nightflyer88/CG_scale/data/CG_scale_mechanics.png

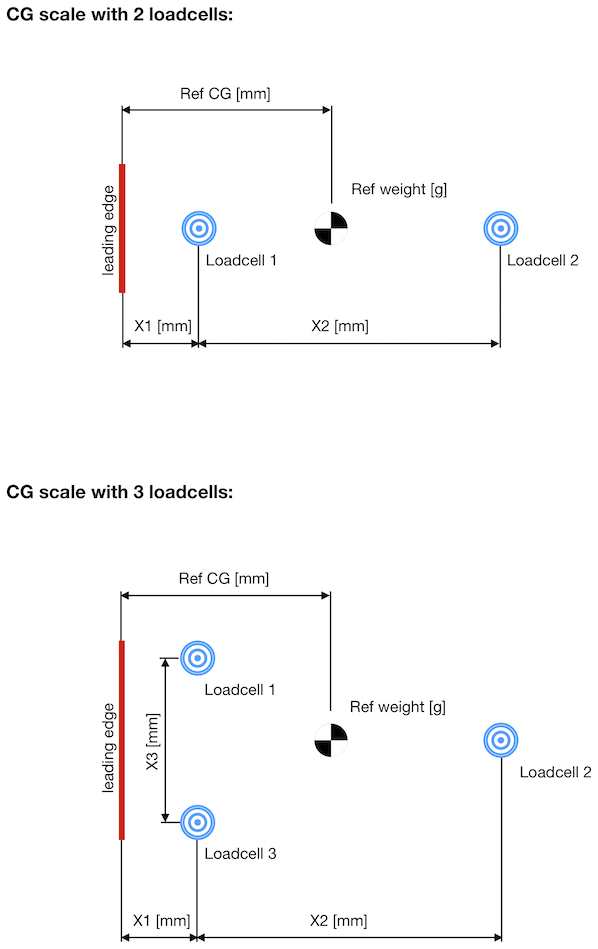
data/CG_scale_mechanics.png
