nightflyer88/CG_scale/data/pc6.png

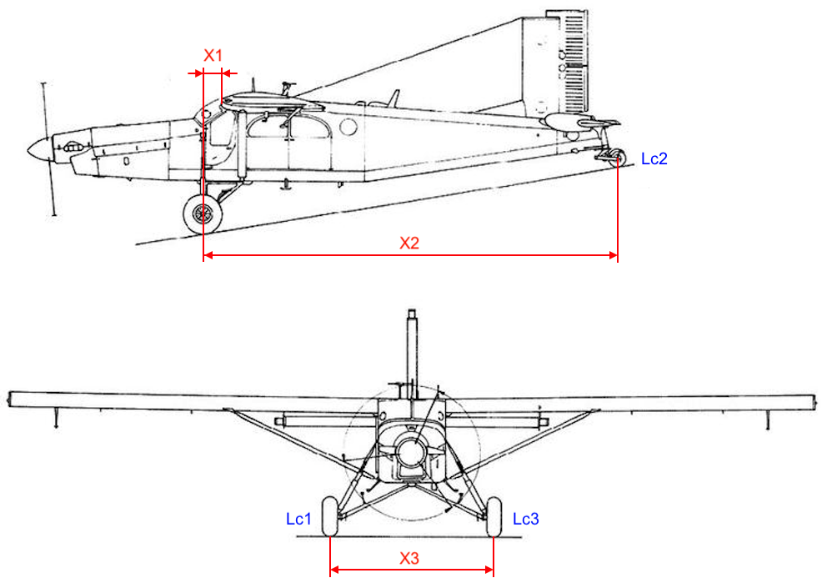
data/pc6.png
