nightflyer88/CG_scale/data/pc7.png

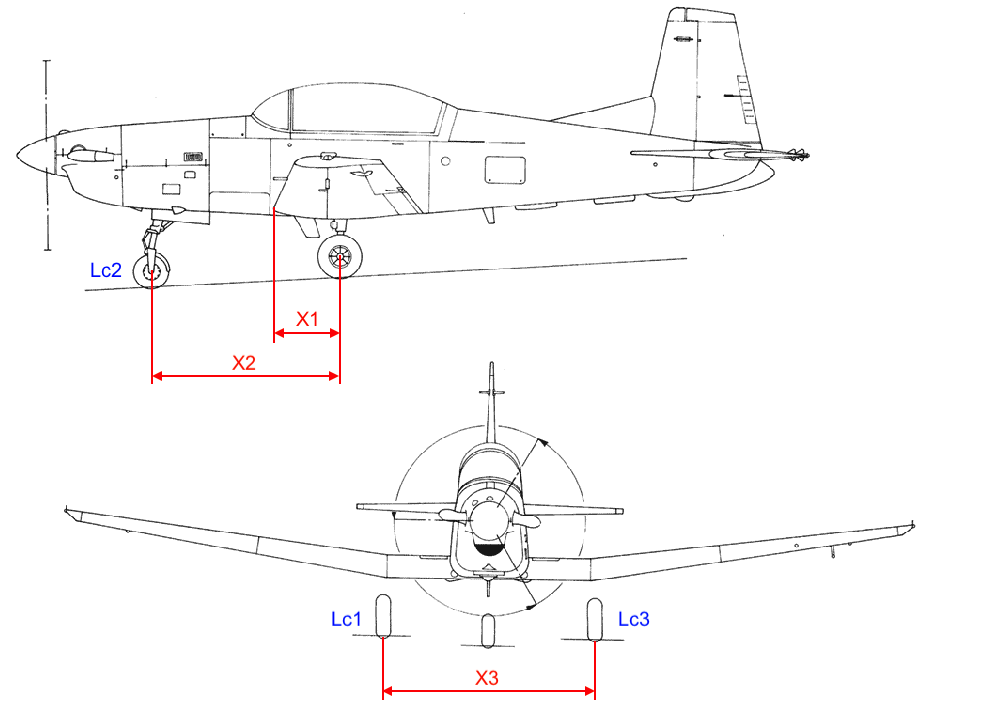
data/pc7.png
