nightflyer88/CG_scale/data/Resistor.png

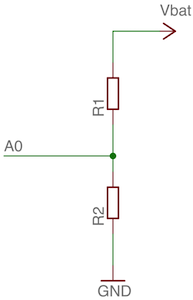
data/Resistor.png
