nightflyer88/CG_scale/Doc/Balance CPT 5mm/img/20180502_205738.jpg

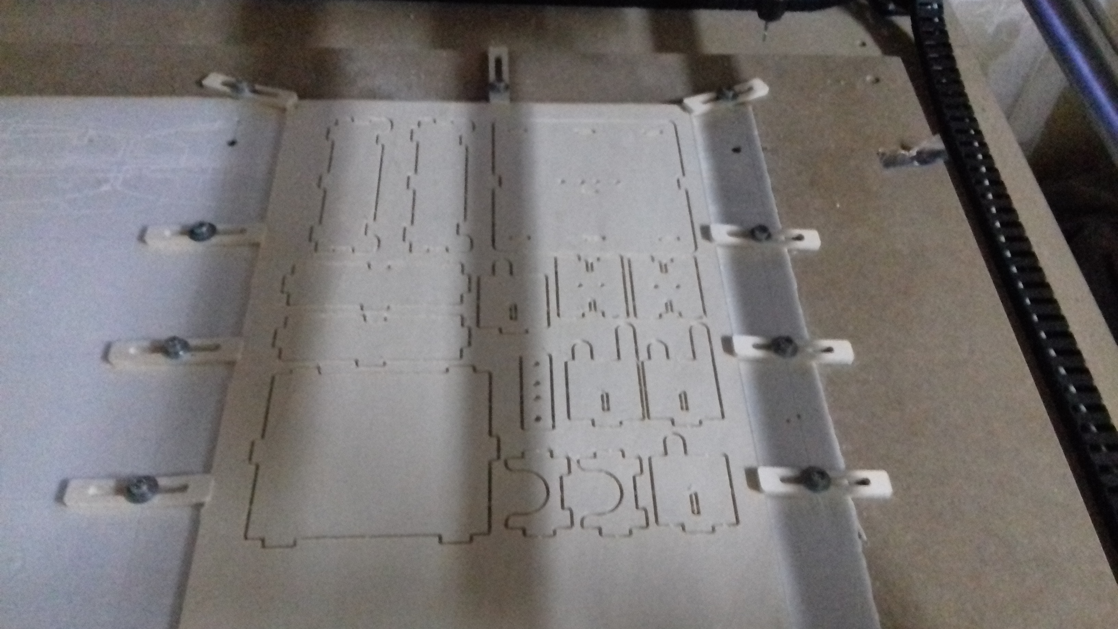
Doc/Balance CPT 5mm/img/20180502_205738.jpg
