nightflyer88/CG_scale/Doc/Balance CPT 5mm/img/20180502_213406.jpg

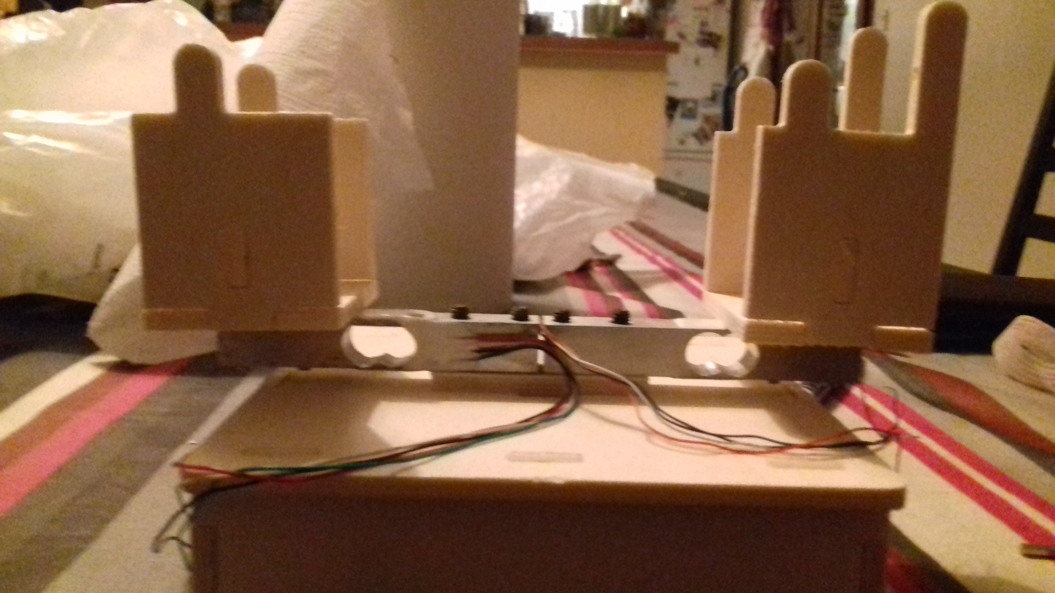
Doc/Balance CPT 5mm/img/20180502_213406.jpg
