nightflyer88/CG_scale/Doc/Balance CPT 5mm/img/20190110_205133.jpg

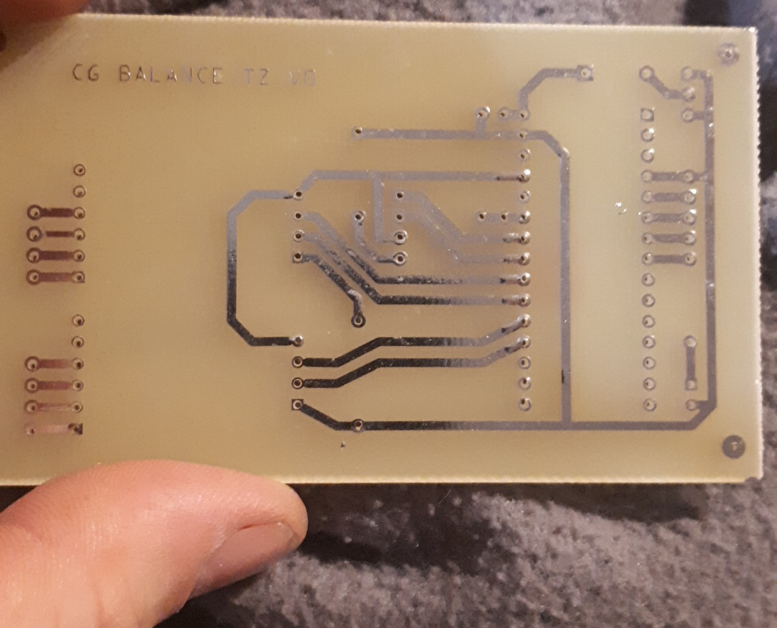
Doc/Balance CPT 5mm/img/20190110_205133.jpg
