nightflyer88/CG_scale/Doc/Balance CPT 5mm/img/20190118_182447.jpg

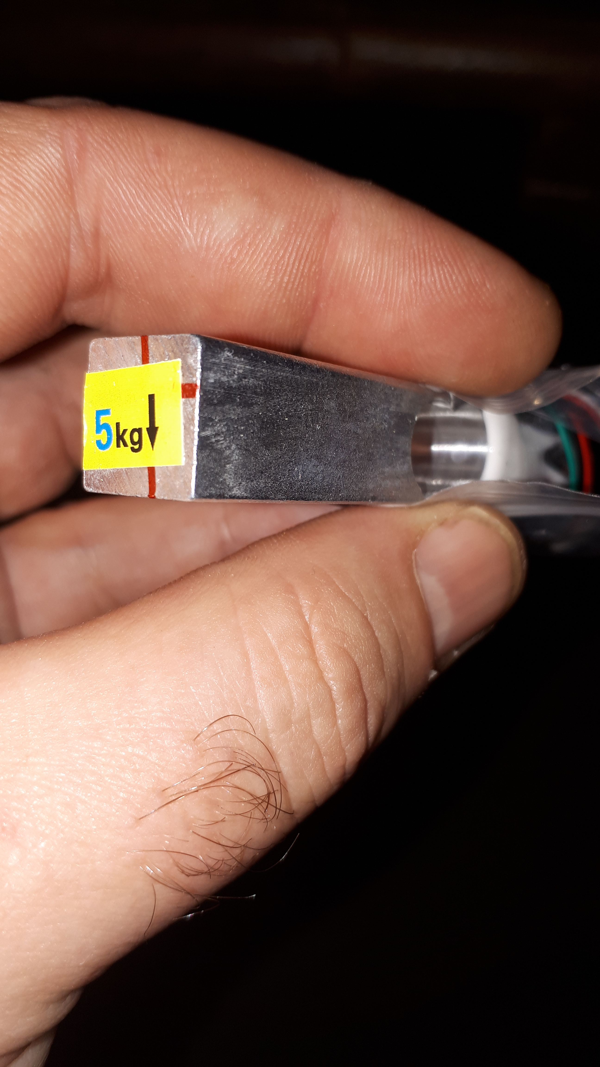
Doc/Balance CPT 5mm/img/20190118_182447.jpg
