nightflyer88/CG_scale/Doc/Balance CPT 5mm/img/20190121_222057.jpg

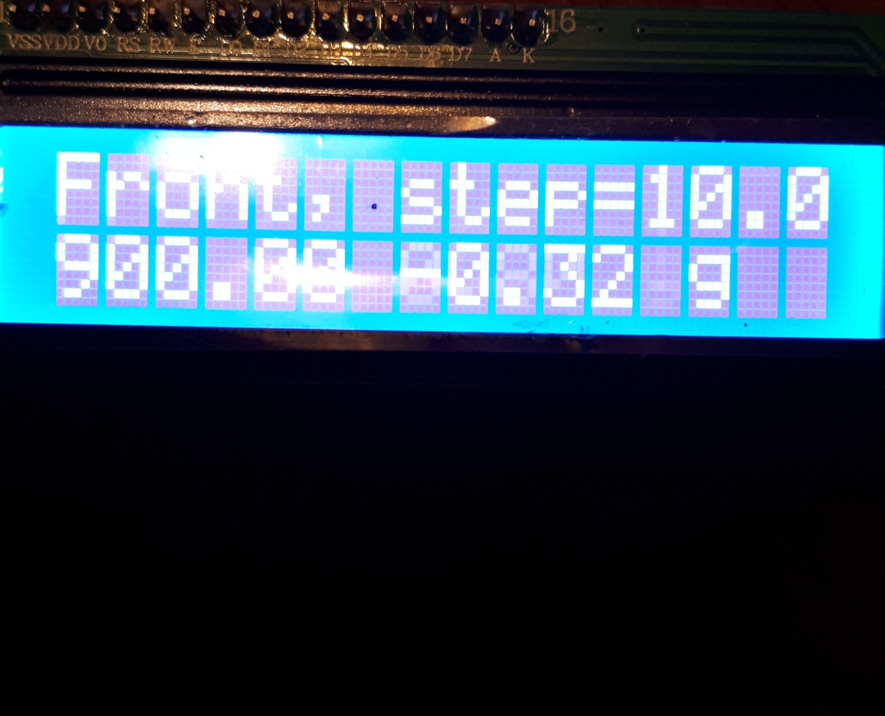
Doc/Balance CPT 5mm/img/20190121_222057.jpg
