nightflyer88/CG_scale/Doc/Balance CPT 5mm/img/20190201_095650.jpg

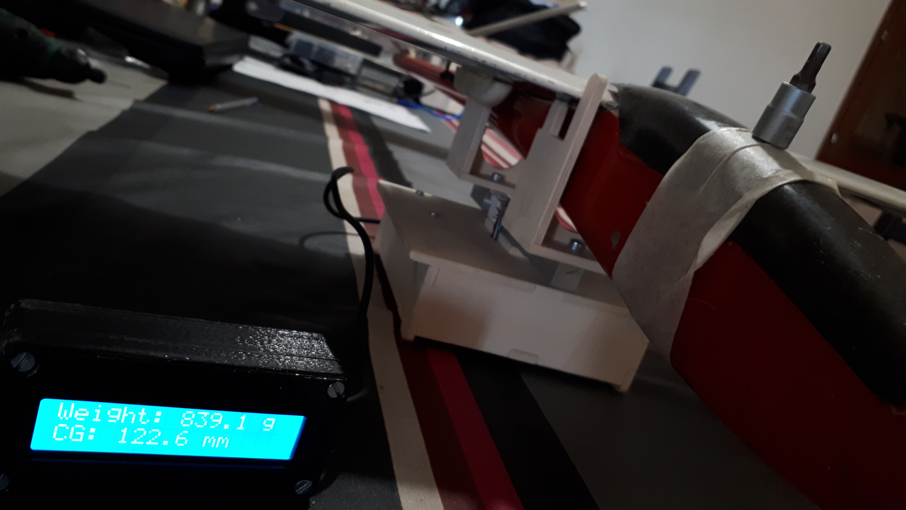
Doc/Balance CPT 5mm/img/20190201_095650.jpg
