nightflyer88/CG_scale/Doc/Balance CPT 5mm/img/20200418_210637.jpg

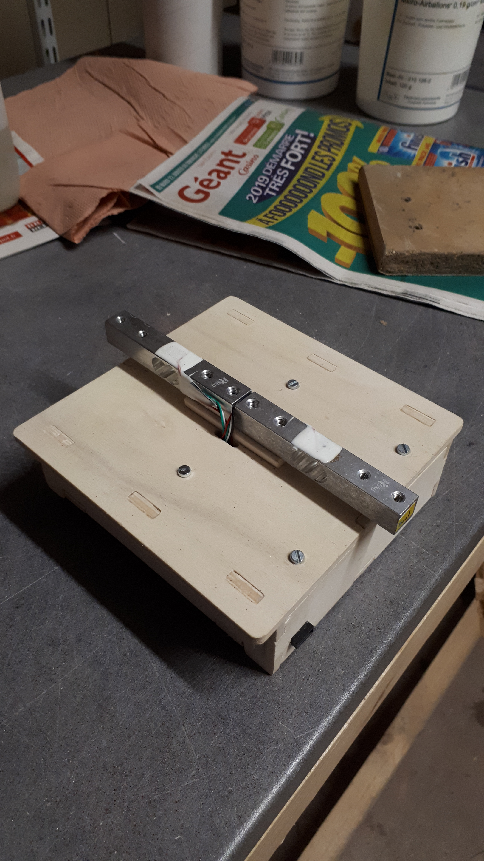
Doc/Balance CPT 5mm/img/20200418_210637.jpg
