nightflyer88/CG_scale/Doc/Balance CPT 5mm/img/20200420_235656.jpg

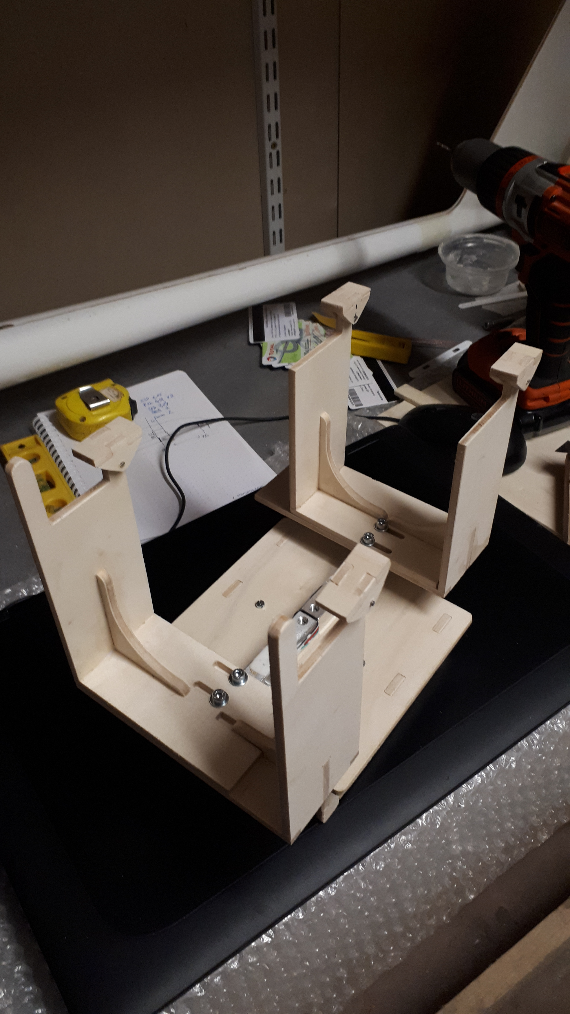
Doc/Balance CPT 5mm/img/20200420_235656.jpg
