nightflyer88/CG_scale/Doc/Balance CPT 5mm/img/20200508_185138.jpg

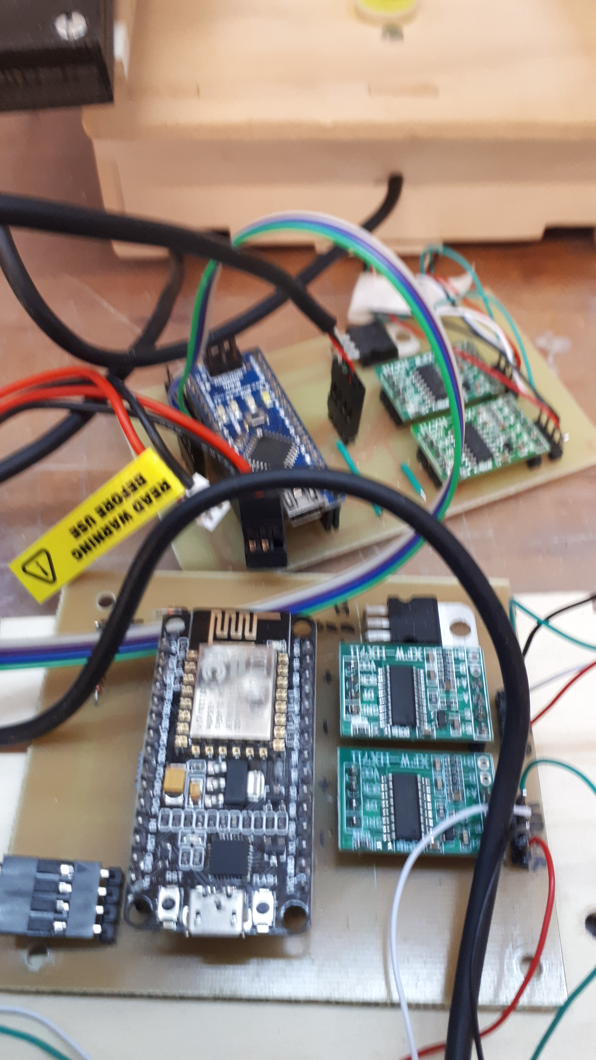
Doc/Balance CPT 5mm/img/20200508_185138.jpg
