nightflyer88/CG_scale/Doc/Fritzing/CG_scale_schema.png

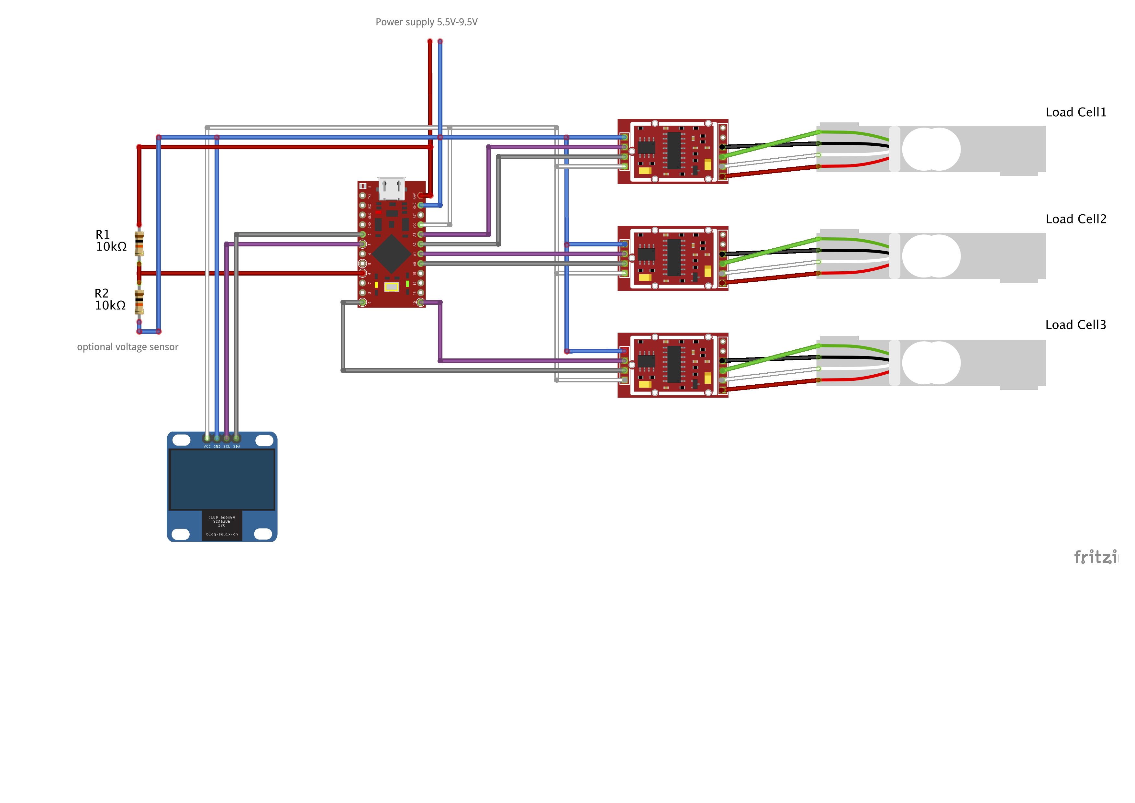
Doc/Fritzing/CG_scale_schema.png
