nightflyer88/CG_scale/Doc/Fritzing/CG_scale_schema_ESP8266.png

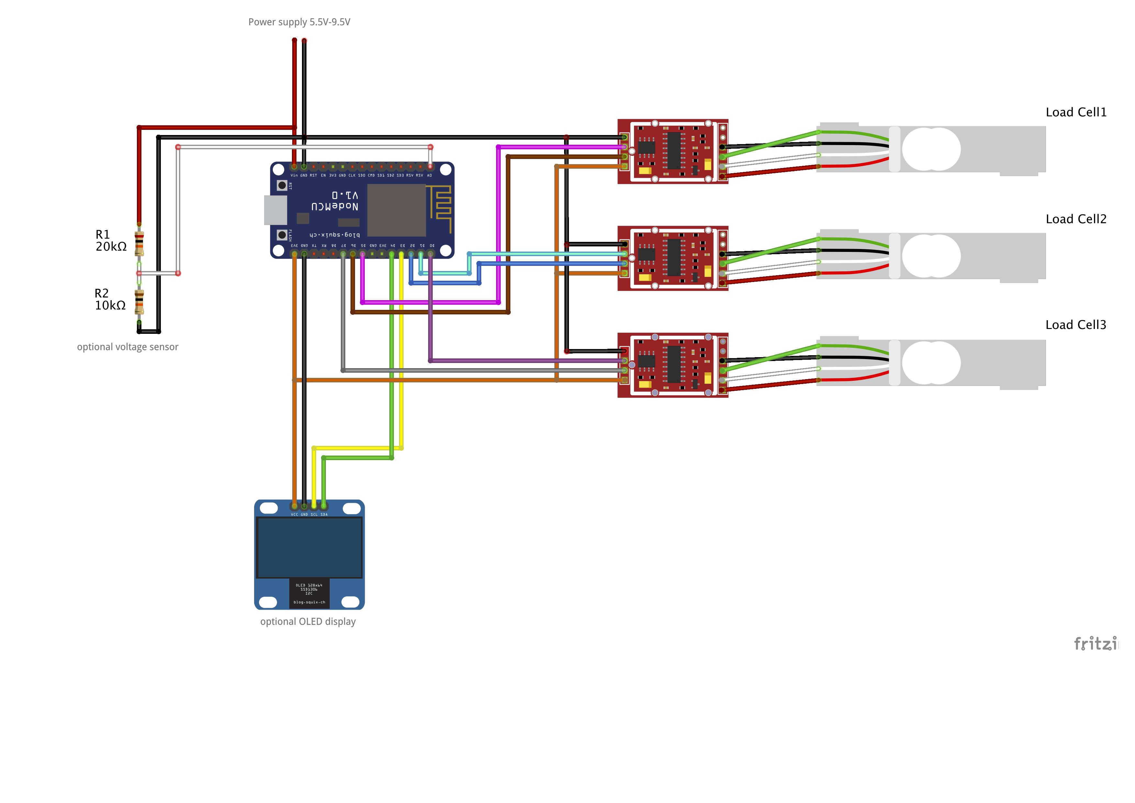
Doc/Fritzing/CG_scale_schema_ESP8266.png
