nightflyer88/CG_scale/Doc/Fritzing/CG_scale_schema_ESP8266_Mini_.png

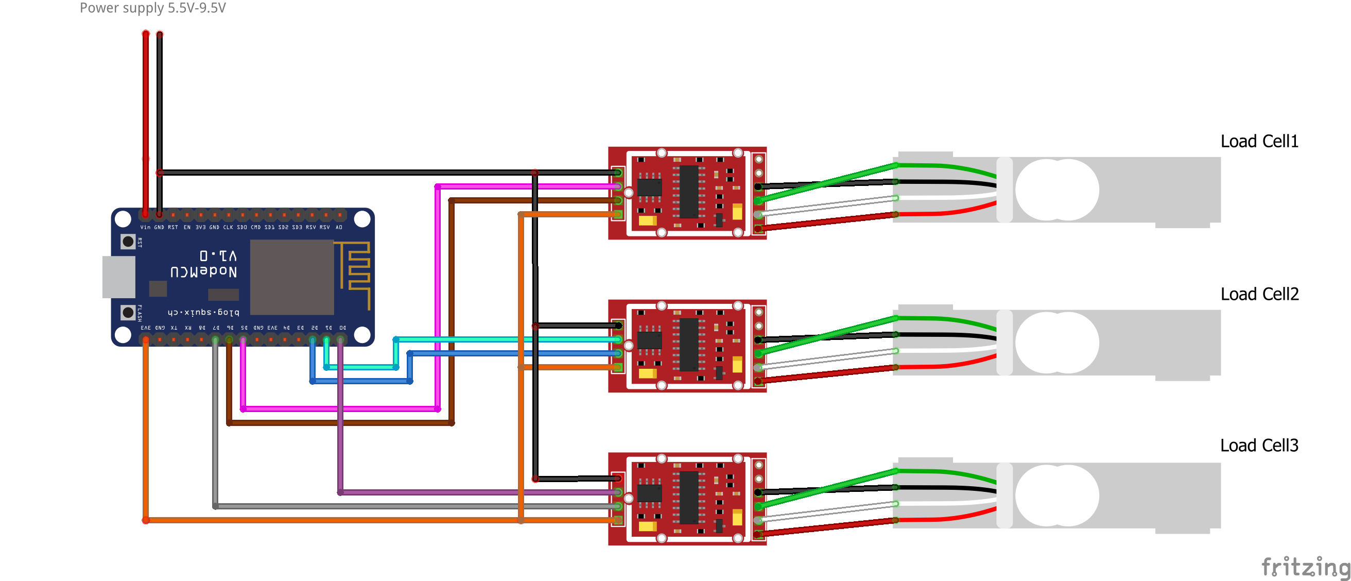
Doc/Fritzing/CG_scale_schema_ESP8266_Mini_.png
