nightflyer88/CG_scale/Doc/Fritzing/CG_scale_schema_ESP8266_PCB.png

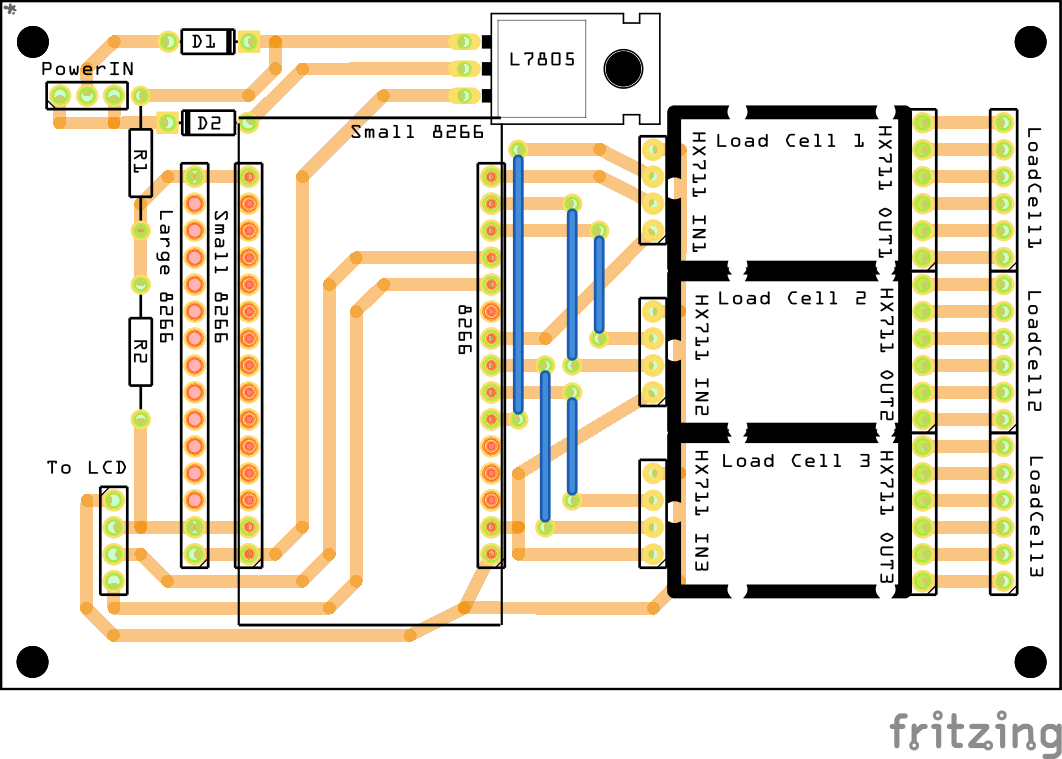
Doc/Fritzing/CG_scale_schema_ESP8266_PCB.png
