nightflyer88/CG_scale/Doc/Fritzing/img/20200415_172140.jpg

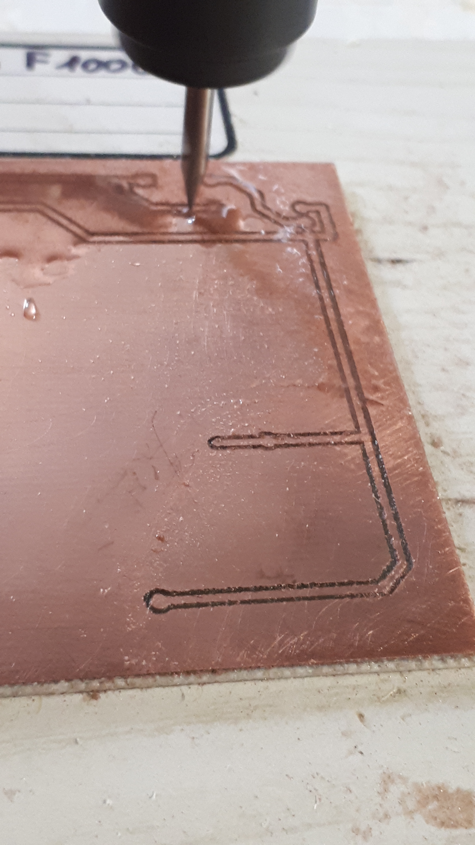
Doc/Fritzing/img/20200415_172140.jpg
