nightflyer88/CG_scale/Doc/Fritzing/img/20200415_210745.jpg

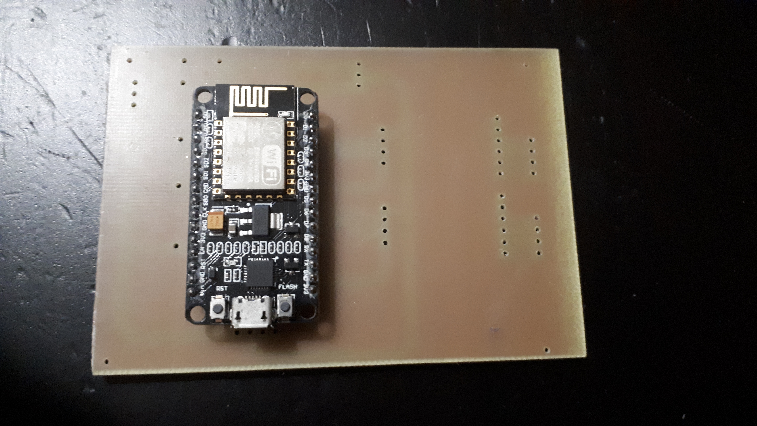
Doc/Fritzing/img/20200415_210745.jpg
