nightflyer88/CG_scale/Doc/Fritzing/img/20200415_210758.jpg

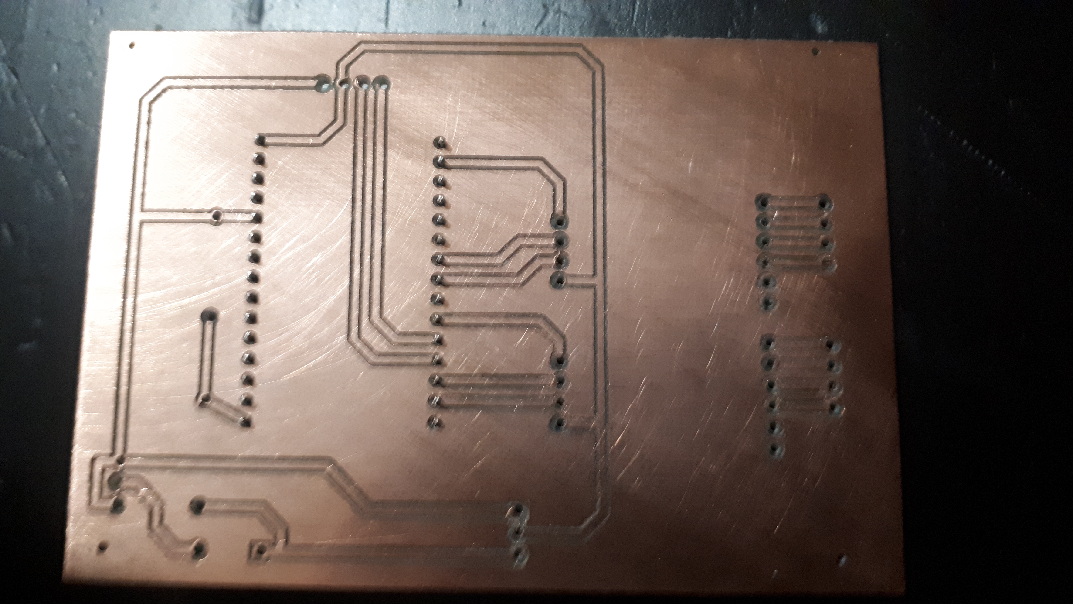
Doc/Fritzing/img/20200415_210758.jpg
