nightflyer88/CG_scale/Doc/Fritzing/img/20200417_173254.jpg

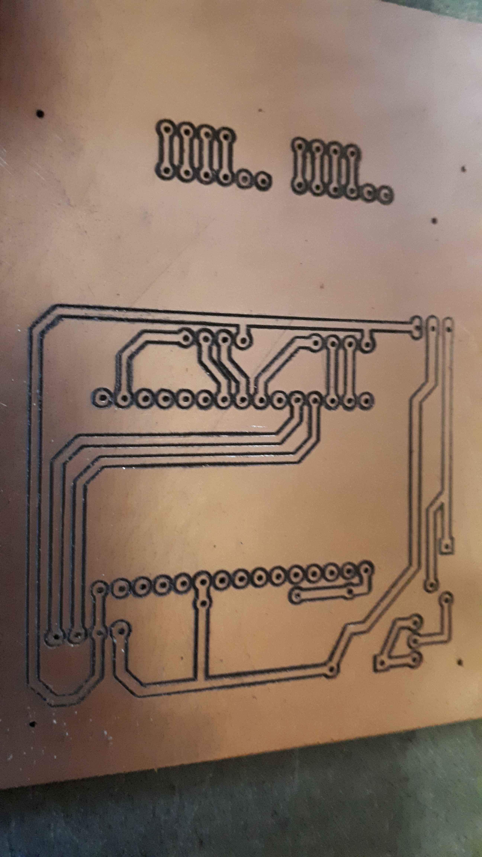
Doc/Fritzing/img/20200417_173254.jpg
