nightflyer88/CG_scale/Doc/Fritzing/img/20200417_190647.jpg

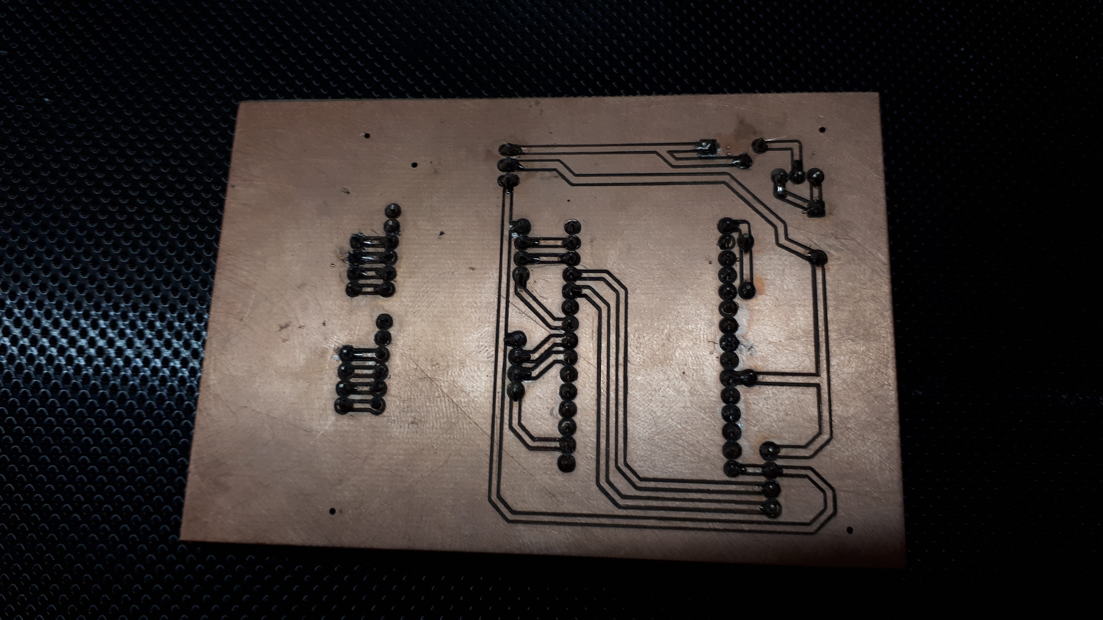
Doc/Fritzing/img/20200417_190647.jpg
