nightflyer88/CG_scale/Doc/img_All/ESP8266_31mm.jpg

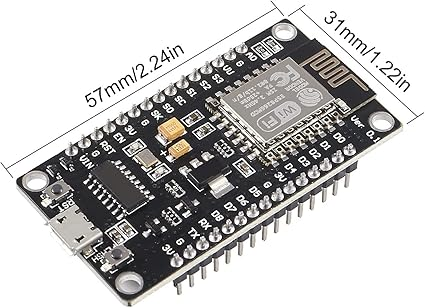
Doc/img_All/ESP8266_31mm.jpg
