nightflyer88/CG_scale/Doc/img_DE/arduino_settings.png

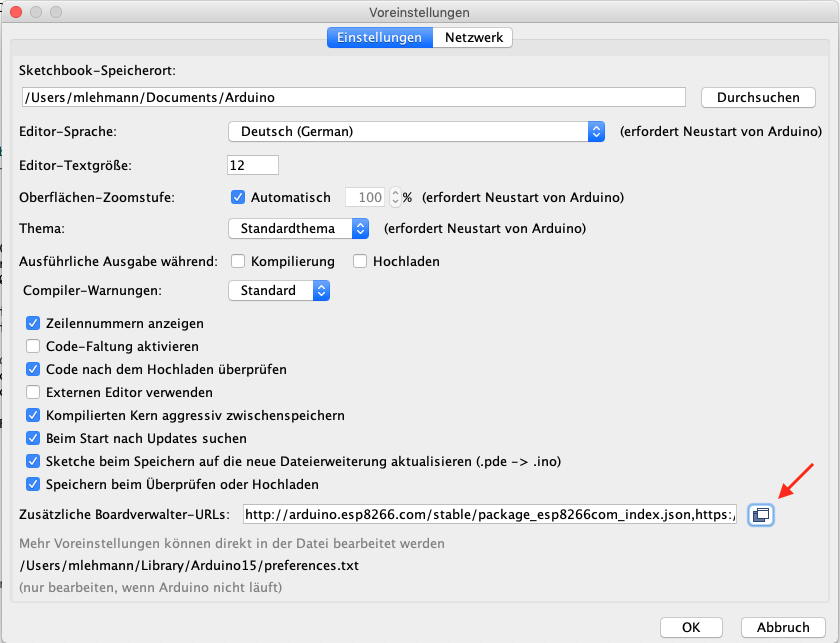
Doc/img_DE/arduino_settings.png
