nightflyer88/CG_scale/Doc/img_DE/arduino_upload.png

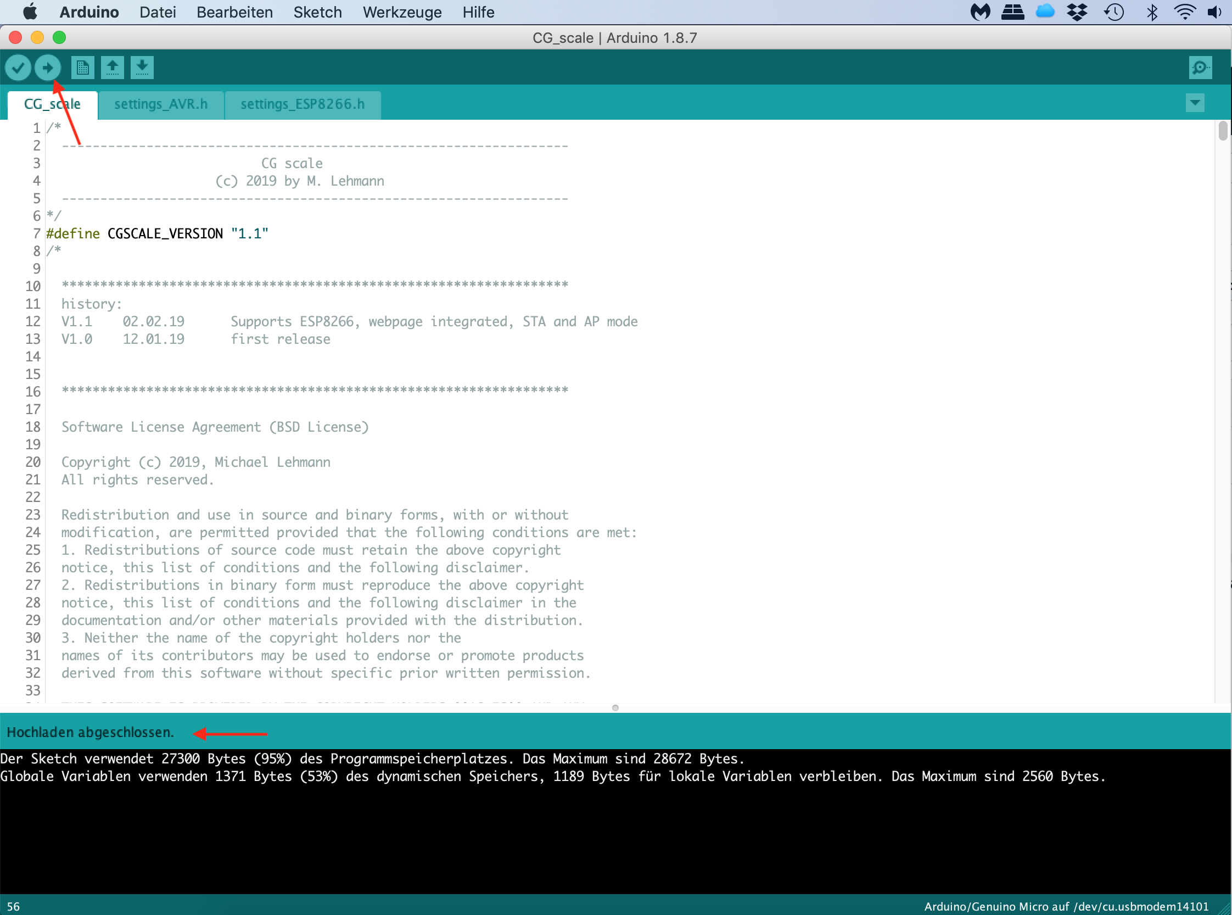
Doc/img_DE/arduino_upload.png
