nightflyer88/CG_scale/Doc/img_DE/board_manager.png

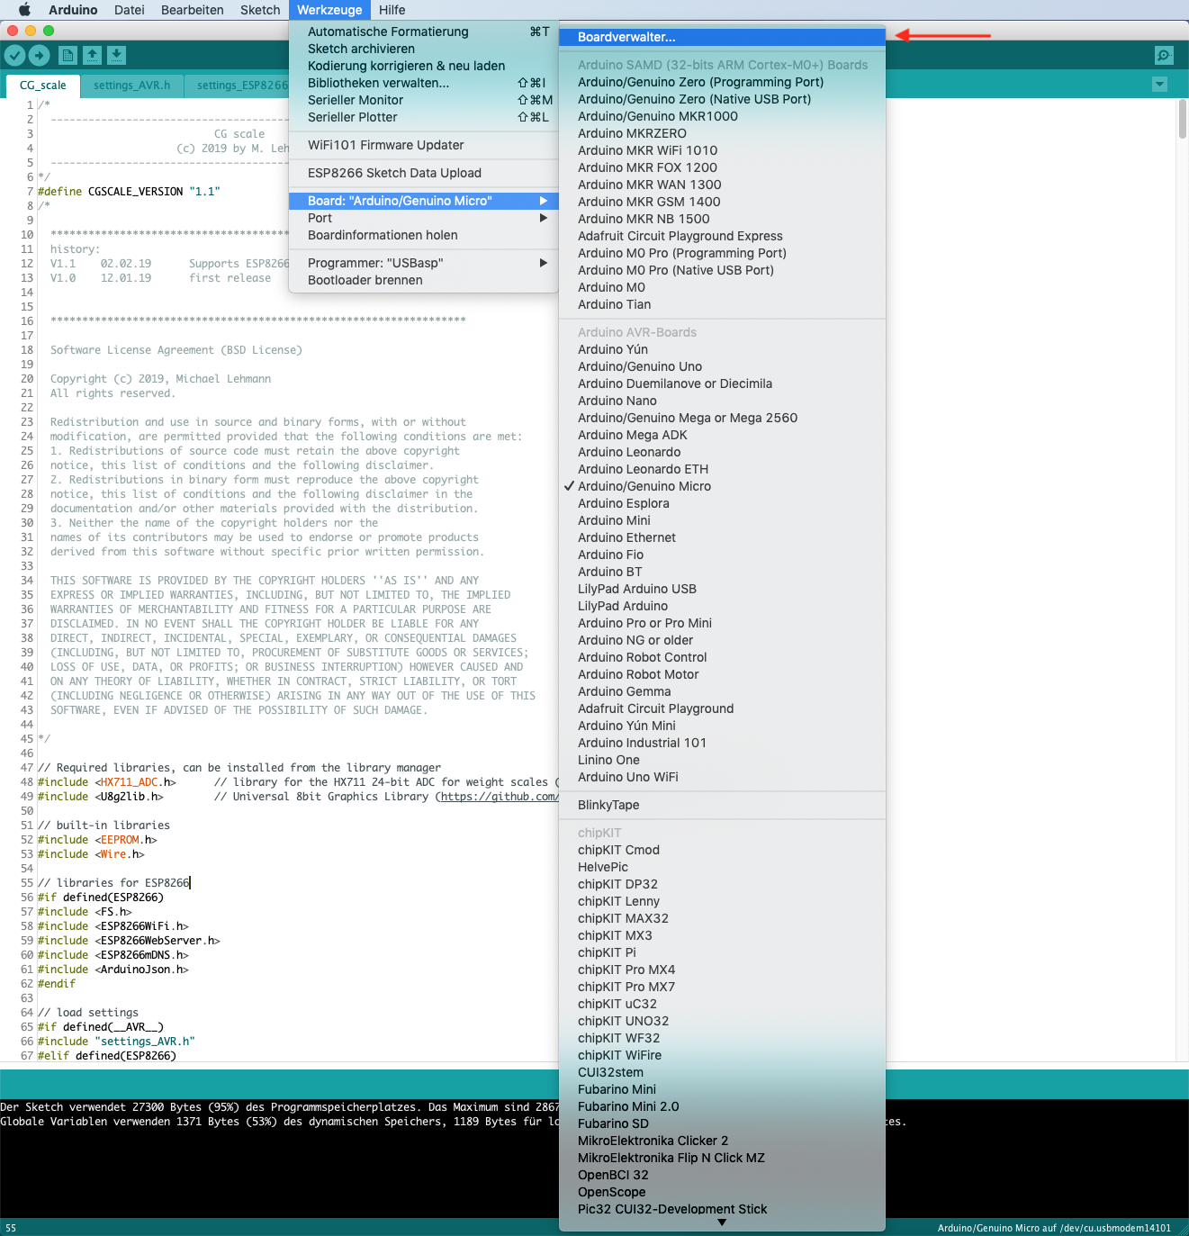
Doc/img_DE/board_manager.png
