nightflyer88/CG_scale/Doc/img_DE/board_url.png

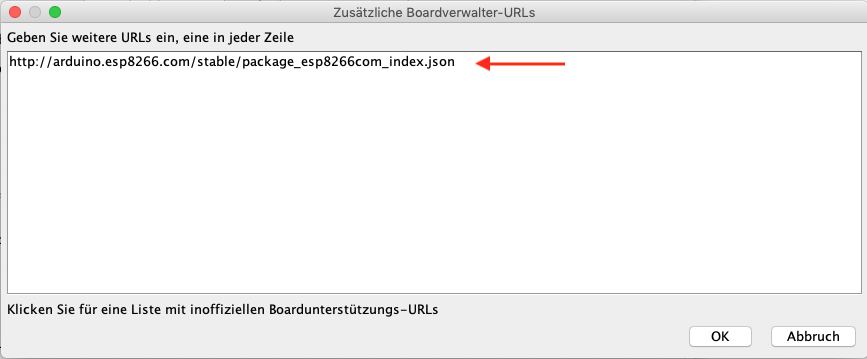
Doc/img_DE/board_url.png
