nightflyer88/CG_scale/Doc/img_DE/cgscale_settings_battery.png

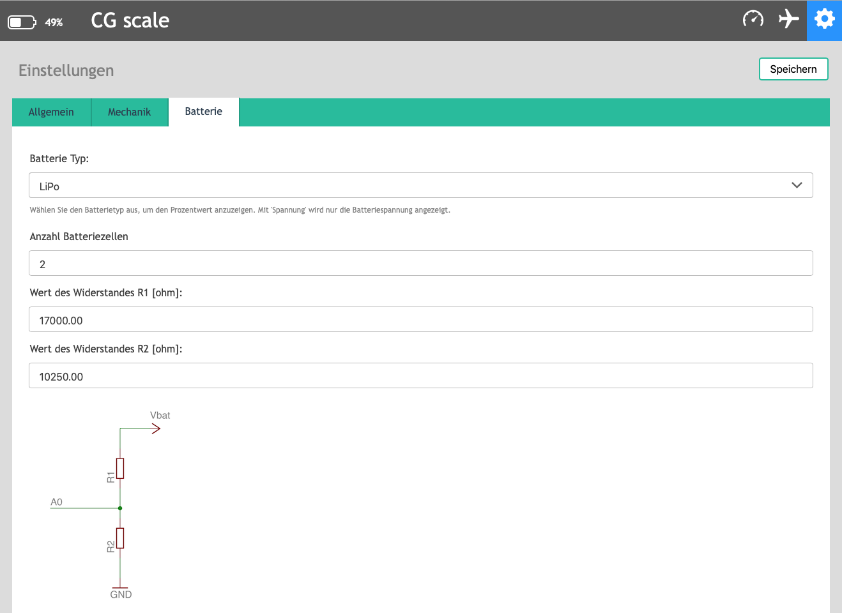
Doc/img_DE/cgscale_settings_battery.png
