nightflyer88/CG_scale/Doc/img_DE/cgscale_V2_homeconfig2.png

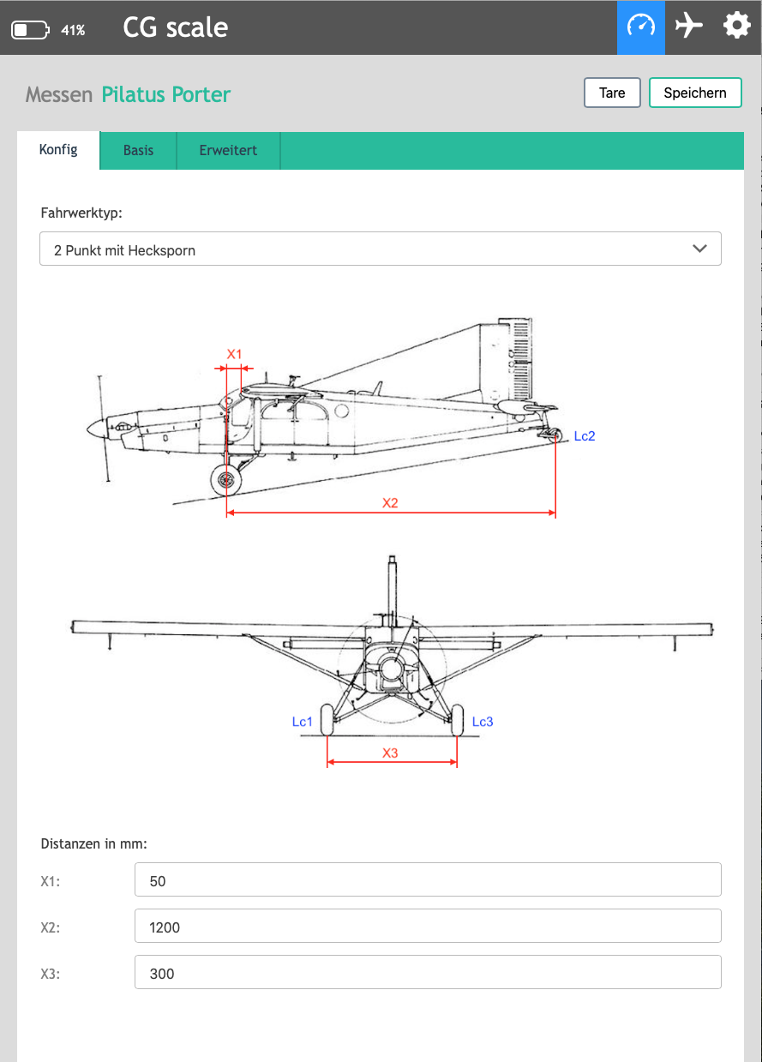
Doc/img_DE/cgscale_V2_homeconfig2.png
