nightflyer88/CG_scale/Doc/img_DE/cgscale_V2_homeext.png

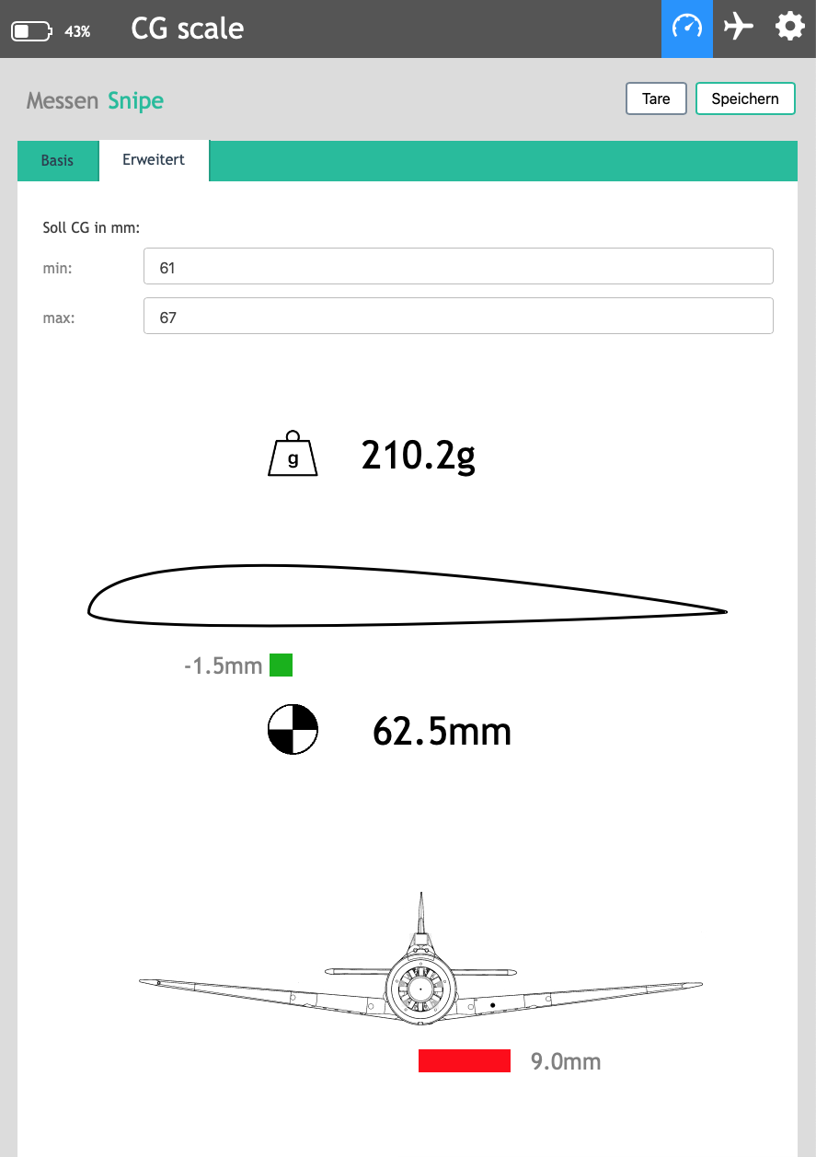
Doc/img_DE/cgscale_V2_homeext.png
