nightflyer88/CG_scale/Doc/img_DE/cgscale_wifisettings.png

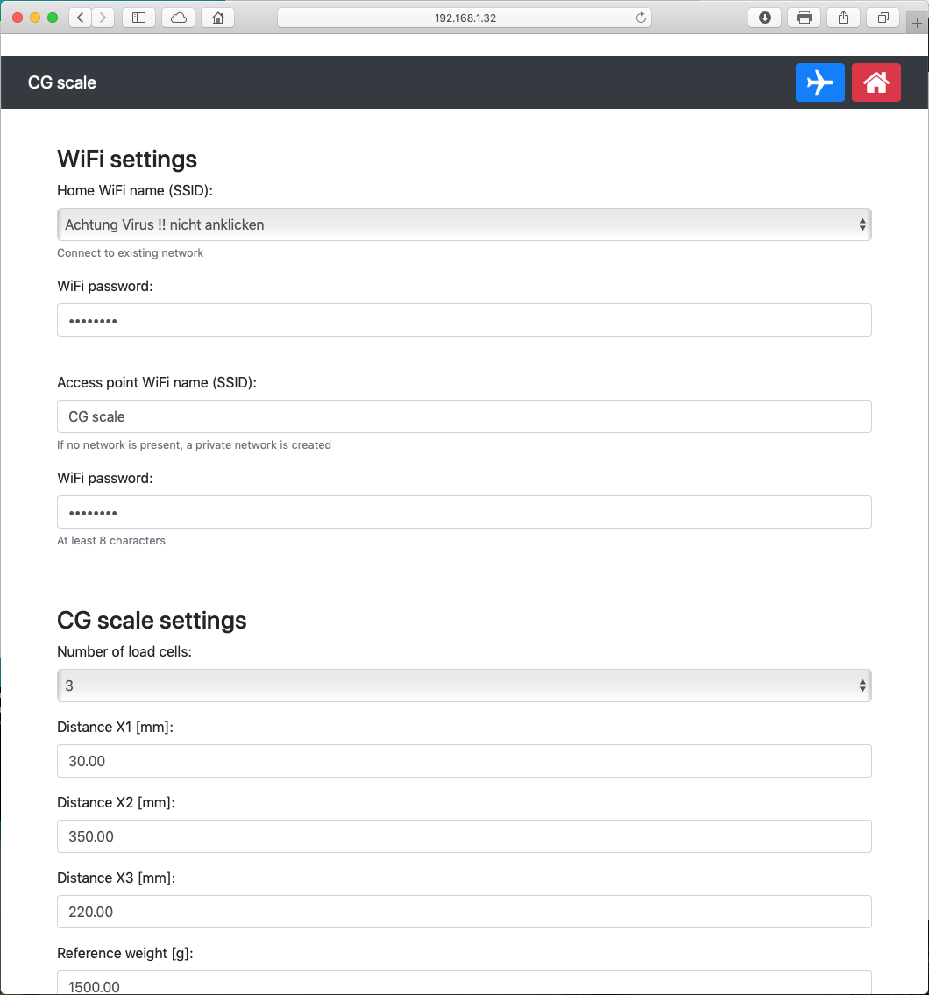
Doc/img_DE/cgscale_wifisettings.png
