nightflyer88/CG_scale/Doc/img_DE/esp8266_board.png

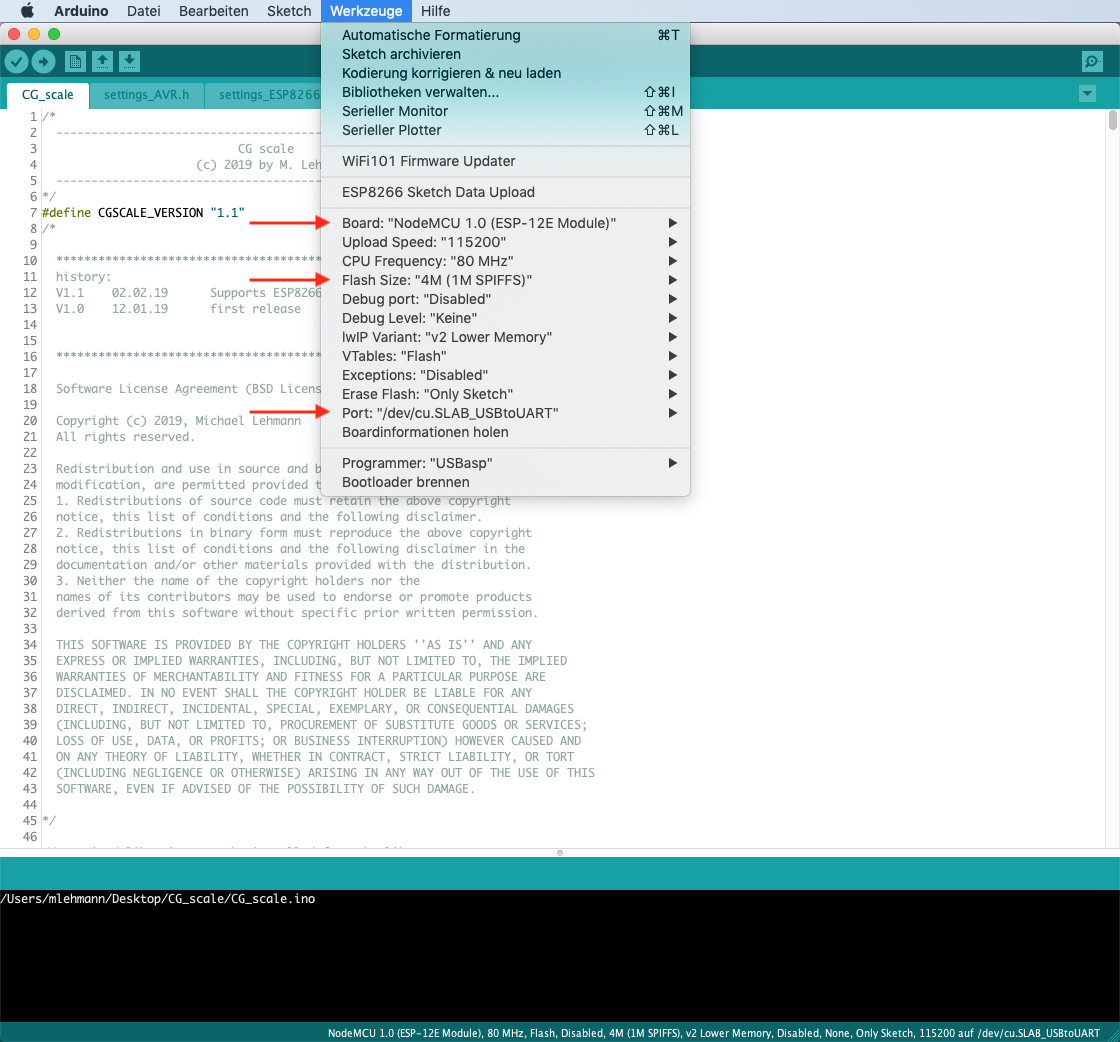
Doc/img_DE/esp8266_board.png
