nightflyer88/CG_scale/Doc/img_DE/esp8266_boardlib.png

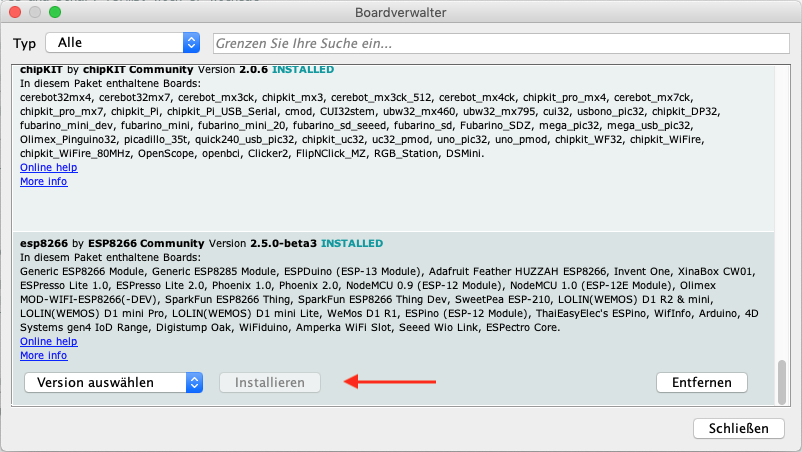
Doc/img_DE/esp8266_boardlib.png
