nightflyer88/CG_scale/Doc/img_DE/esp8266_dataupload.png

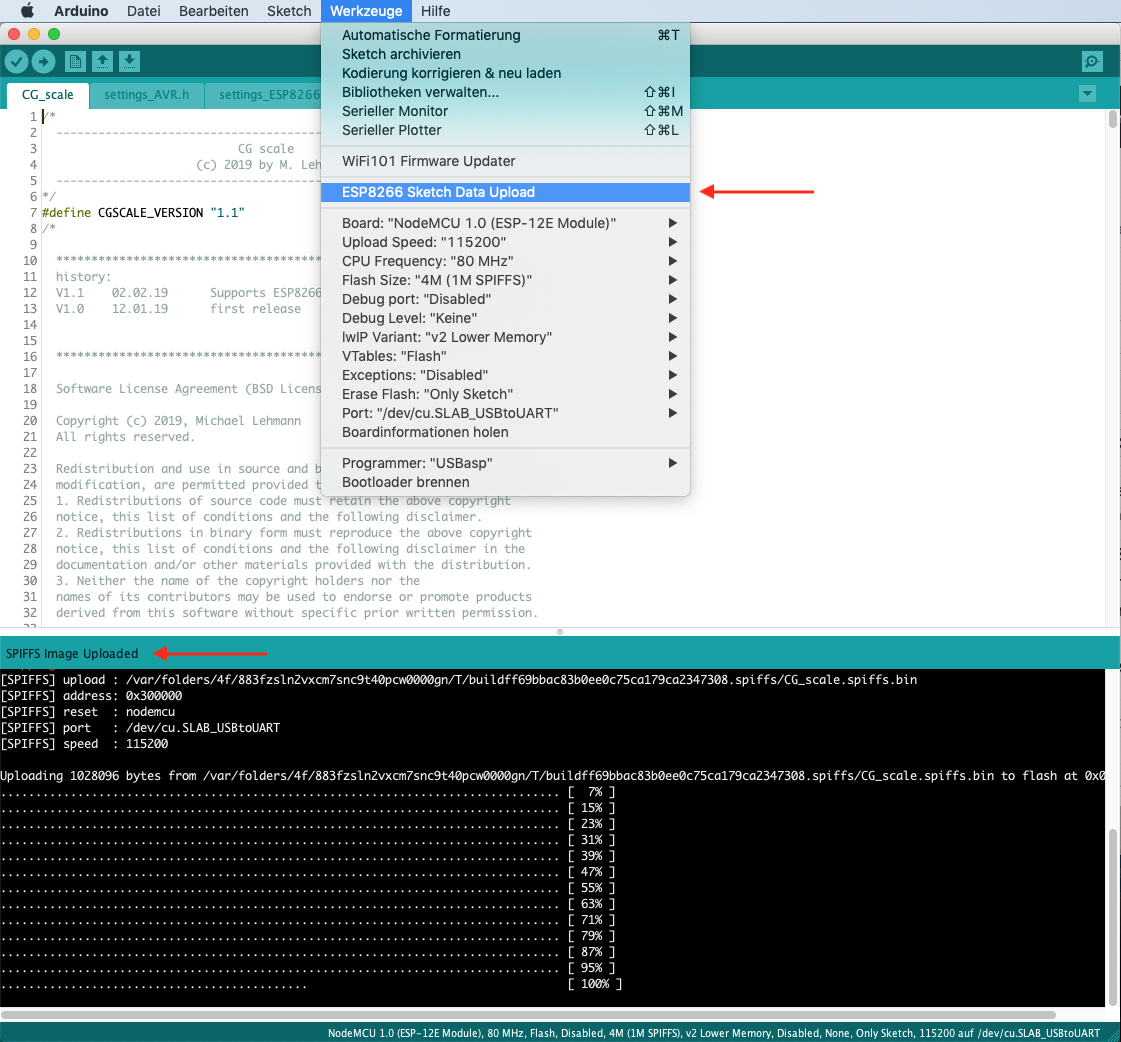
Doc/img_DE/esp8266_dataupload.png
