nightflyer88/CG_scale/Doc/img_DE/esp8266_OTA_port.png

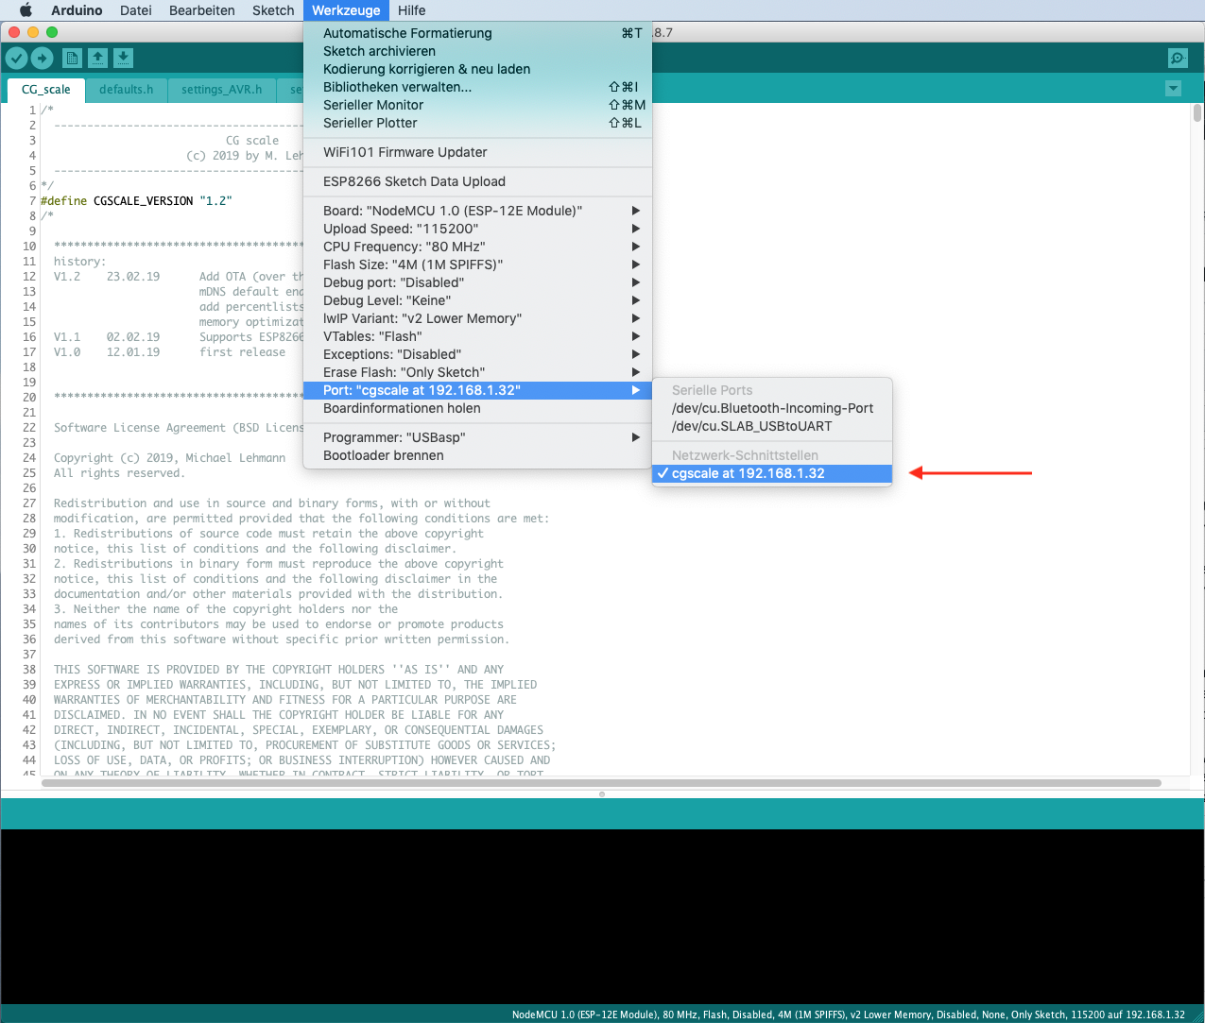
Doc/img_DE/esp8266_OTA_port.png
