nightflyer88/CG_scale/Doc/img_DE/esp8266_upload.png

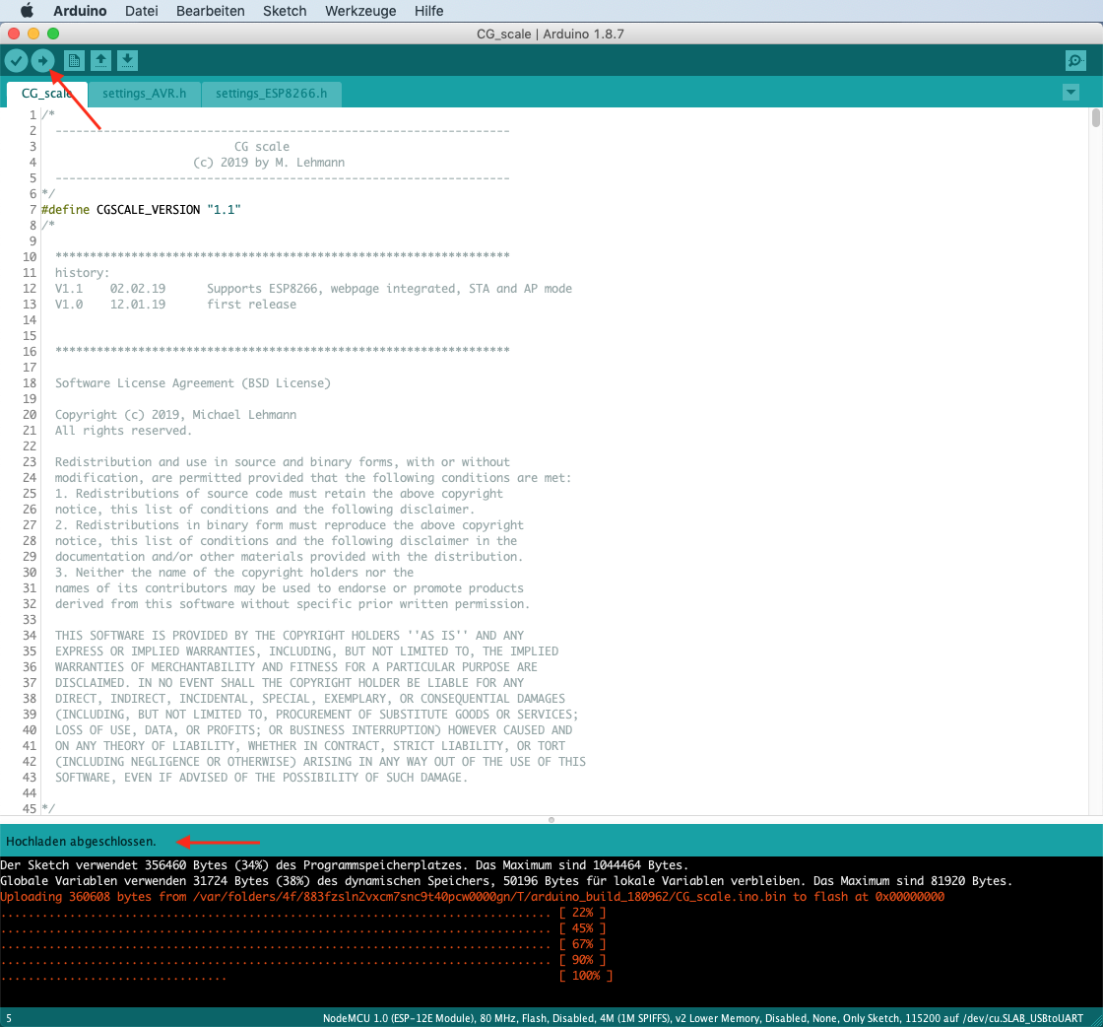
Doc/img_DE/esp8266_upload.png
