nightflyer88/CG_scale/Doc/img_DE/esp_tool.png

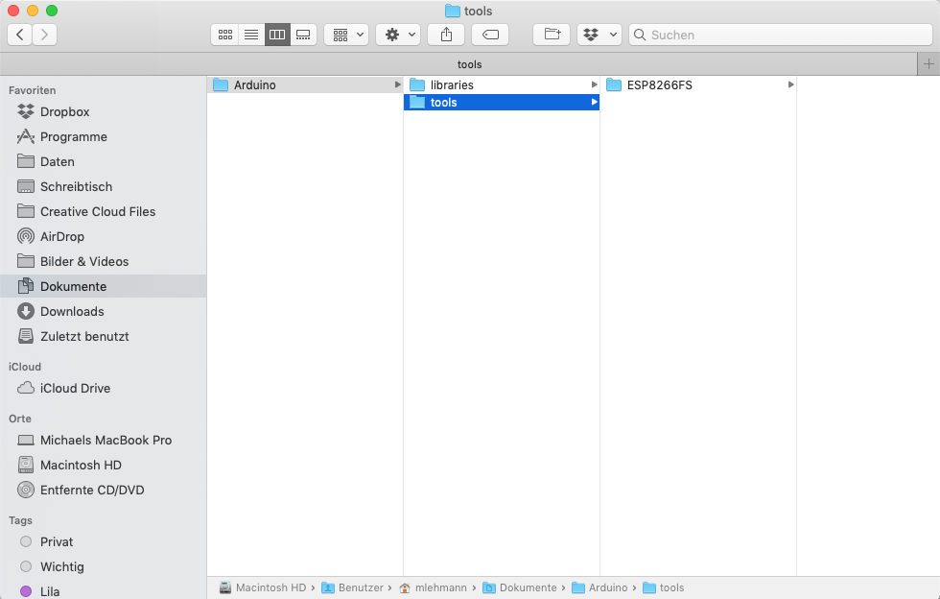
Doc/img_DE/esp_tool.png
