nightflyer88/CG_scale/Doc/img_DE/hx711_lib.png

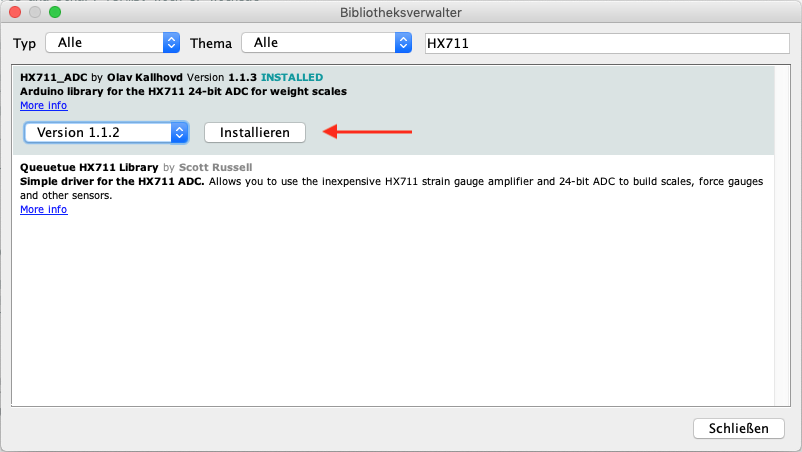
Doc/img_DE/hx711_lib.png
