nightflyer88/CG_scale/Doc/img_DE/json_lib.png

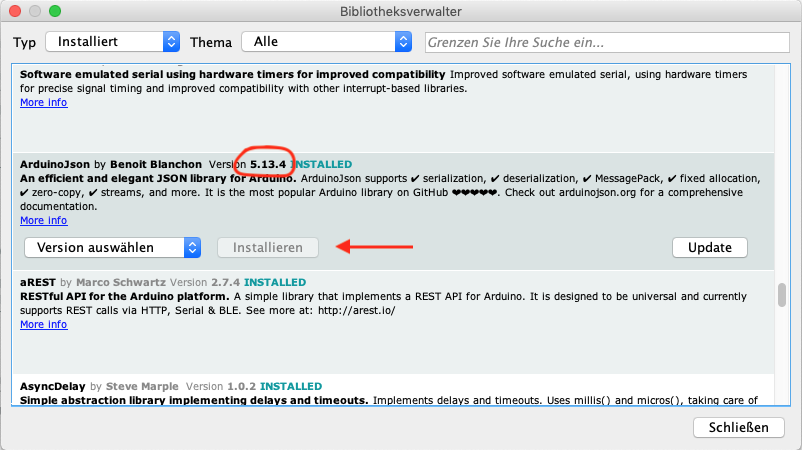
Doc/img_DE/json_lib.png
