nightflyer88/CG_scale/Doc/img_DE/json_lib_V2.png

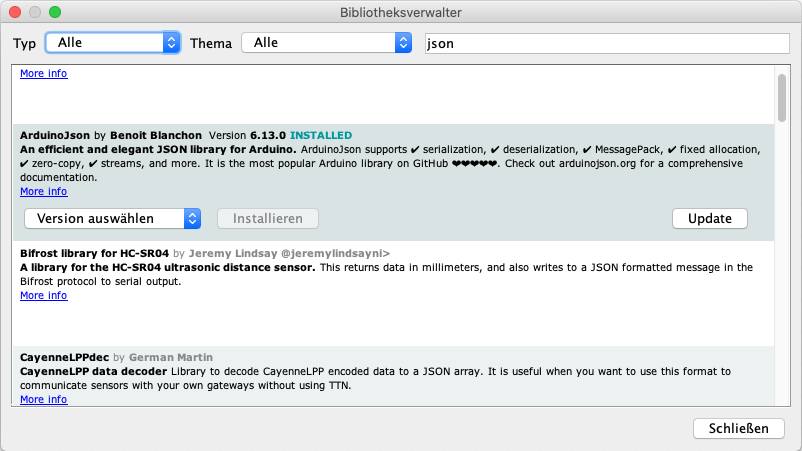
Doc/img_DE/json_lib_V2.png
