nightflyer88/CG_scale/Doc/img_DE/lib_manager.png

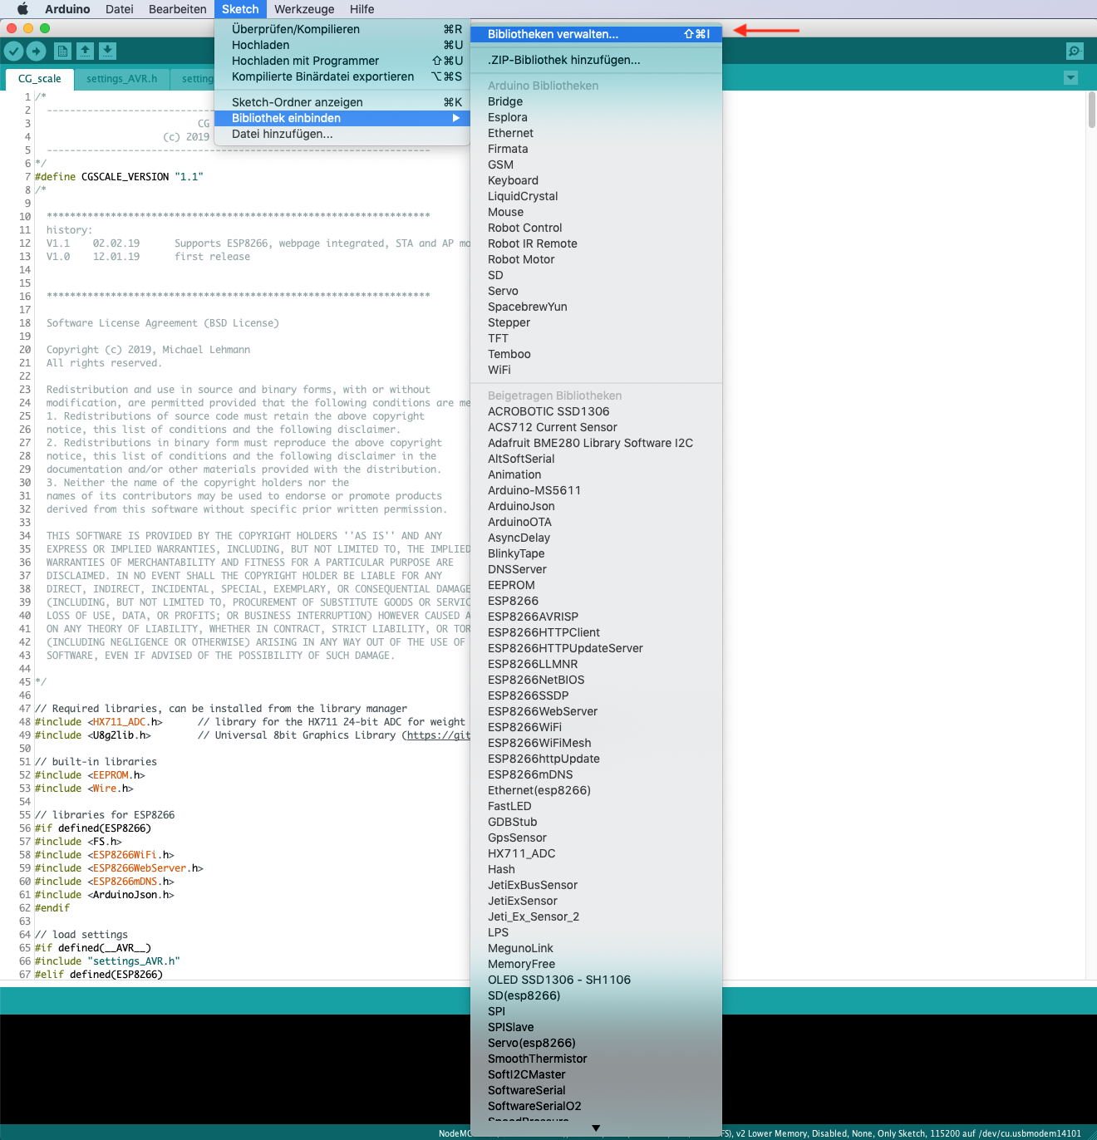
Doc/img_DE/lib_manager.png
