nightflyer88/CG_scale/Doc/img_DE/nodeMCUpyFlasher.png

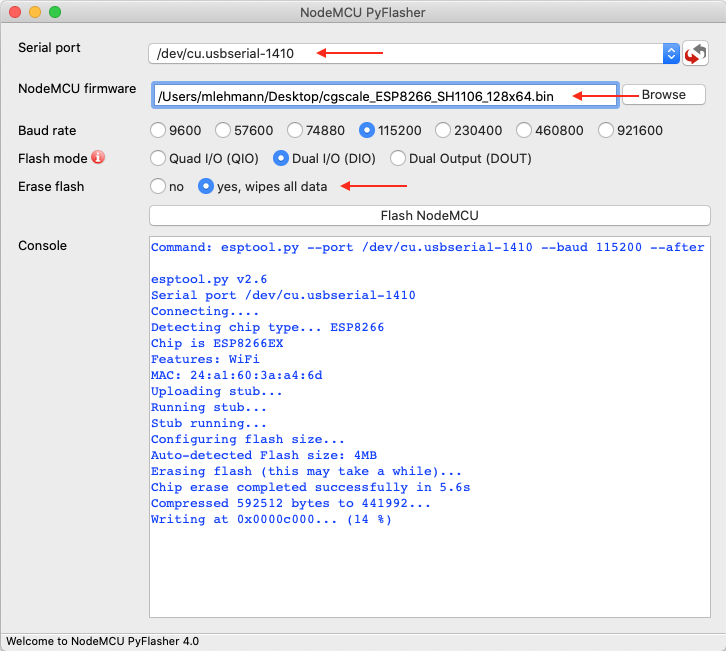
Doc/img_DE/nodeMCUpyFlasher.png
