nightflyer88/CG_scale/Doc/img_DE/serial_menu.png

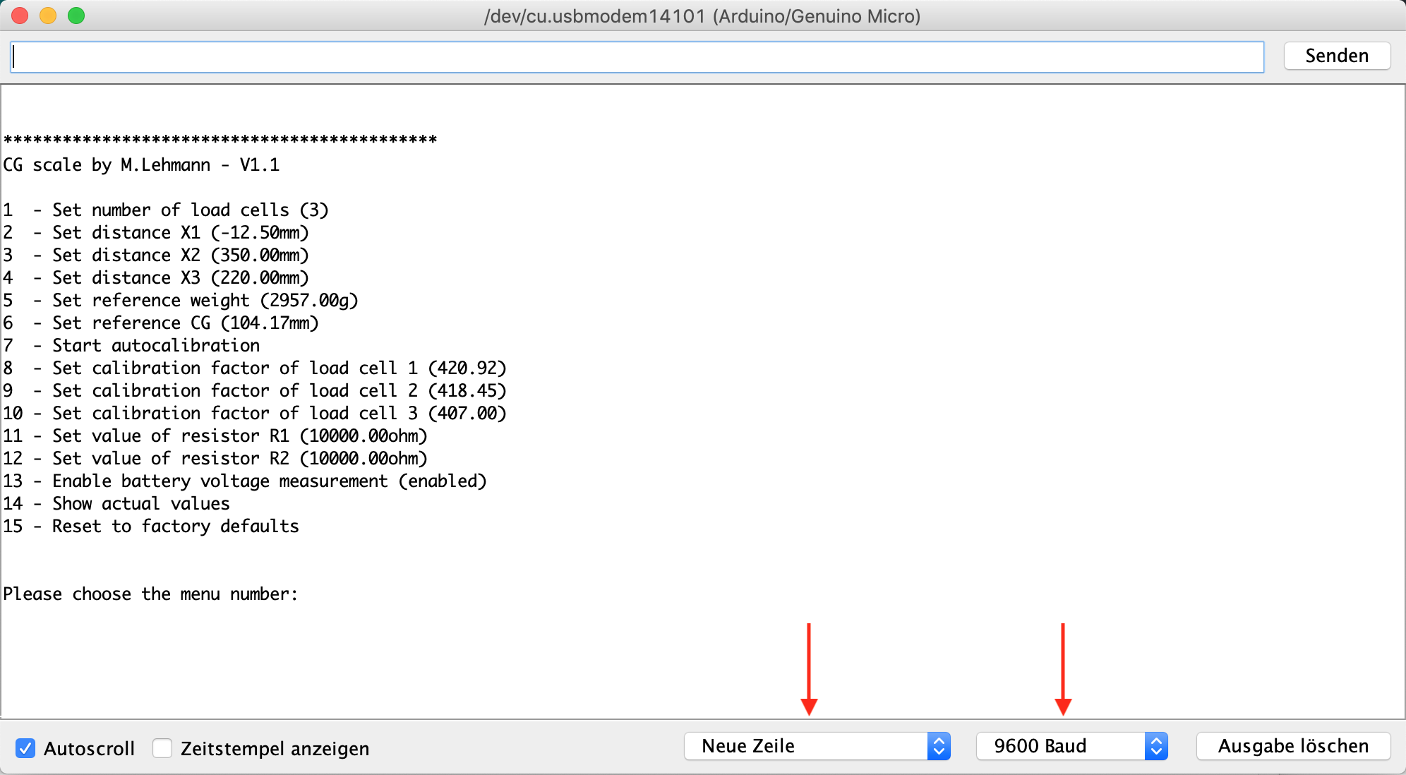
Doc/img_DE/serial_menu.png
