nightflyer88/CG_scale/Doc/img_DE/u8g2_lib.png

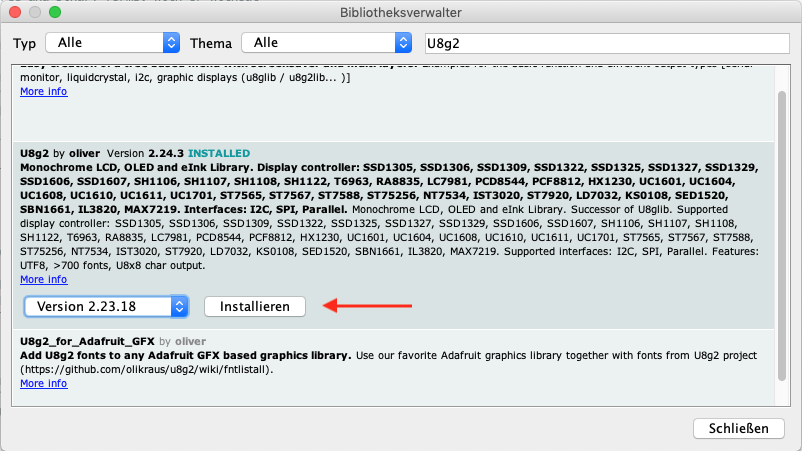
Doc/img_DE/u8g2_lib.png
