nightflyer88/CG_scale/Doc/img_DE/webupdate.png

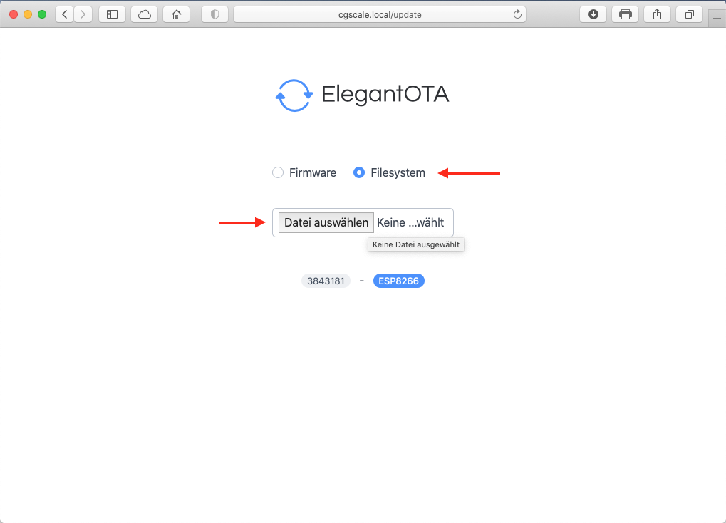
Doc/img_DE/webupdate.png
