nightflyer88/CG_scale/Doc/img_DE/webupdate_progress.png

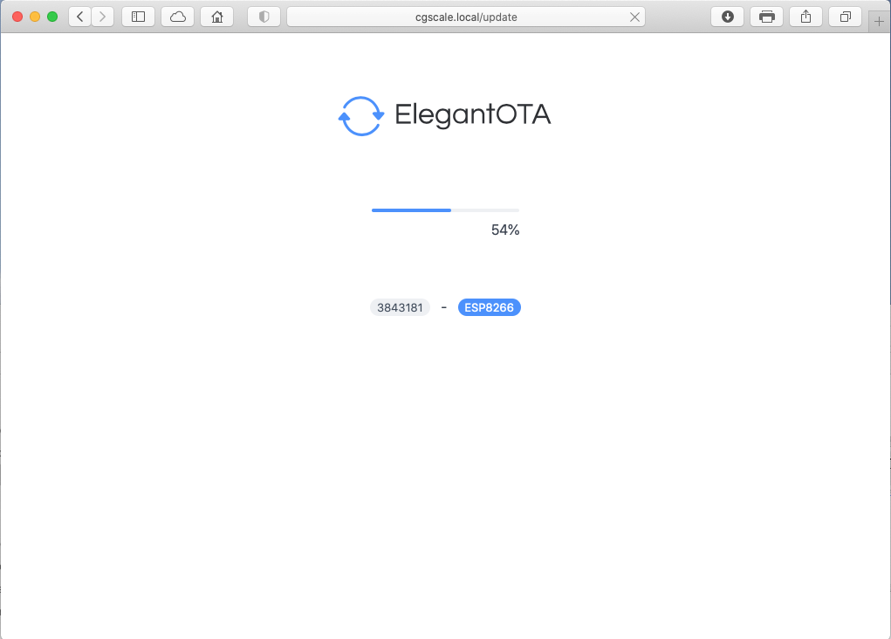
Doc/img_DE/webupdate_progress.png
