nightflyer88/CG_scale/Doc/img_EN/arduino_settings.png

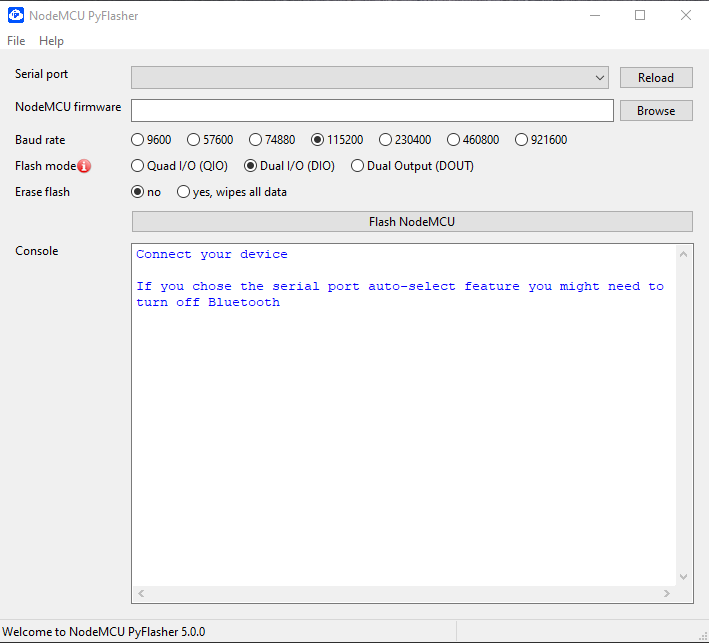
Doc/img_EN/arduino_settings.png
