nightflyer88/CG_scale/Doc/Oled BOX/img/Freecad 3D.jpg

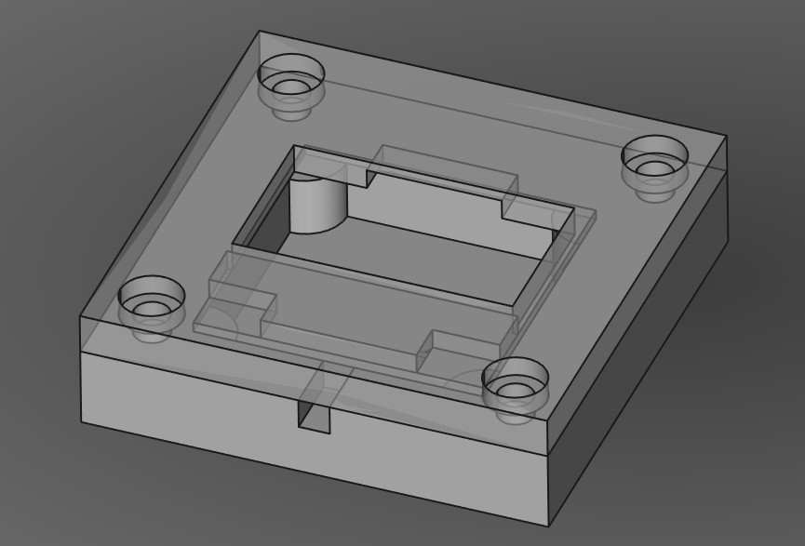
Doc/Oled BOX/img/Freecad 3D.jpg
