nightflyer88/CG_scale/Doc/Oled BOX/img/Screen 2.jpg

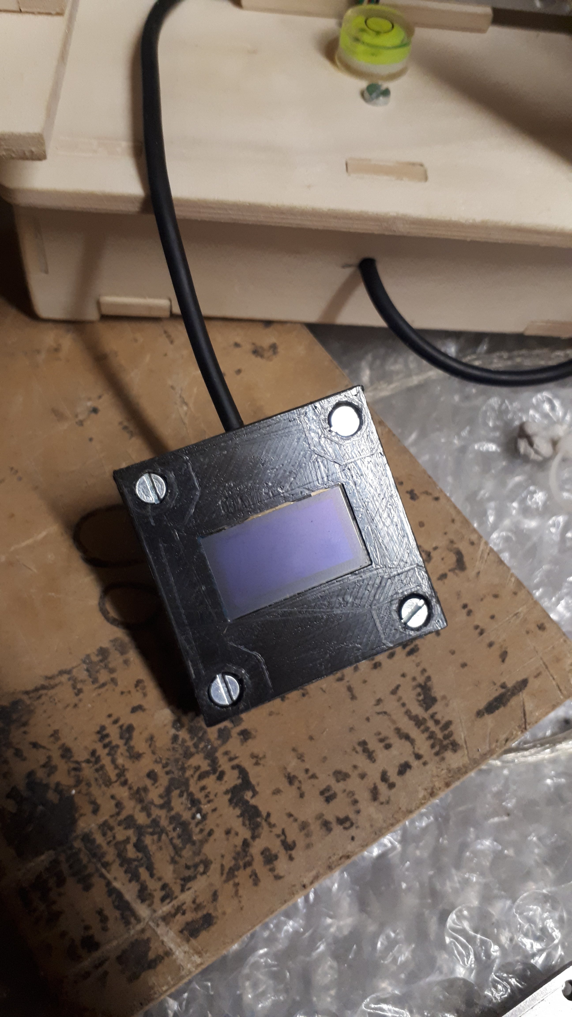
Doc/Oled BOX/img/Screen 2.jpg
