nightflyer88/CG_scale/Doc/Oled BOX/img/Screen .jpg

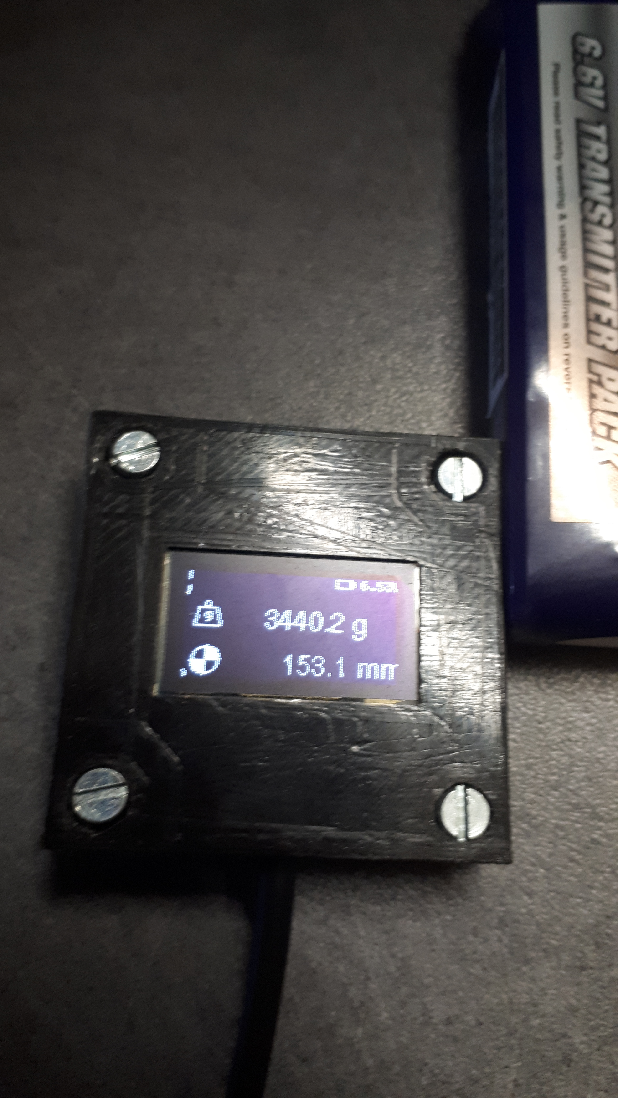
Doc/Oled BOX/img/Screen .jpg
