nightflyer88/CG_scale/img/airplane.png

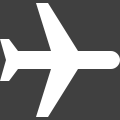
img/airplane.png
