nightflyer88/CG_scale/img/settings.png

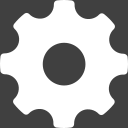
img/settings.png
