nightflyer88/CG_scale/Doc/Fritzing/Production PCB/CG_scale_schema_ESP8266_PCB_etch_mask_bottom_mirror.pdf

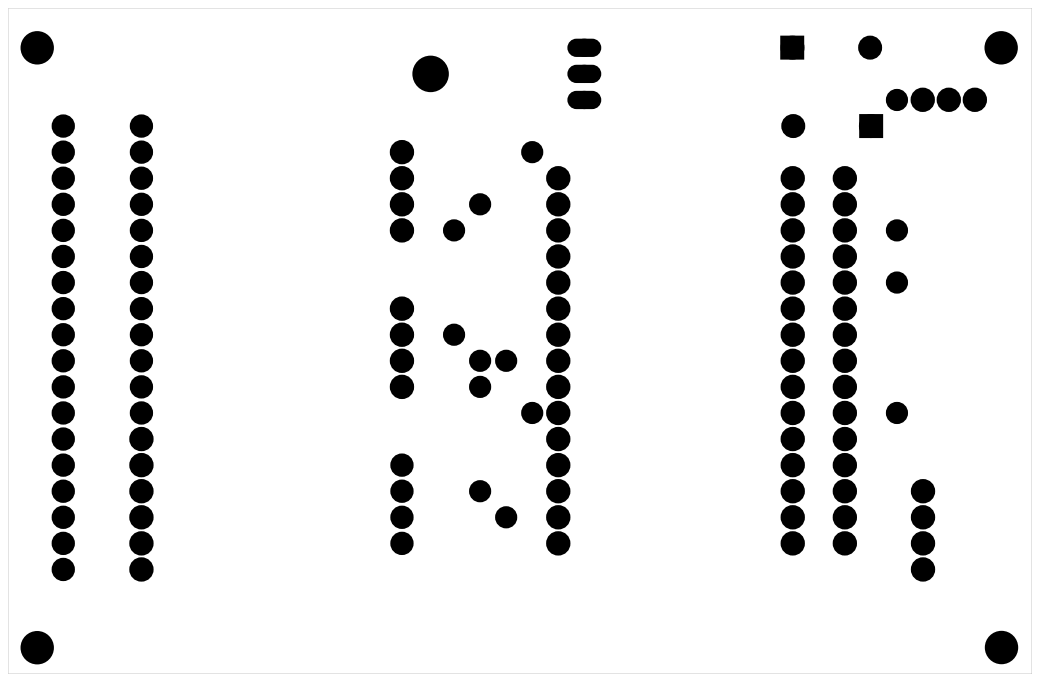
[picture p94: page 1]
