nightflyer88/CG_scale/Doc/Fritzing/Production PCB/CG_scale_schema_ESP8266_PCB_etch_mask_top_mirror.pdf

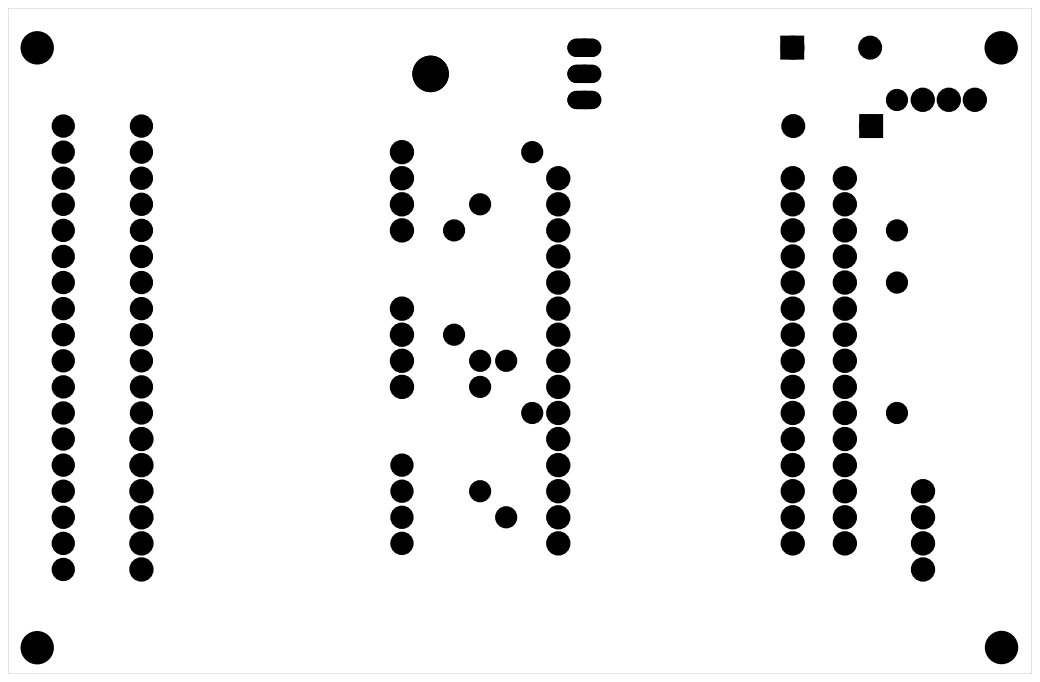
[picture p96: page 1]
