nightflyer88/CG_scale/Doc/Fritzing/Production PCB/CG_scale_schema_ESP8266_PCB_etch_silk_top_mirror.pdf

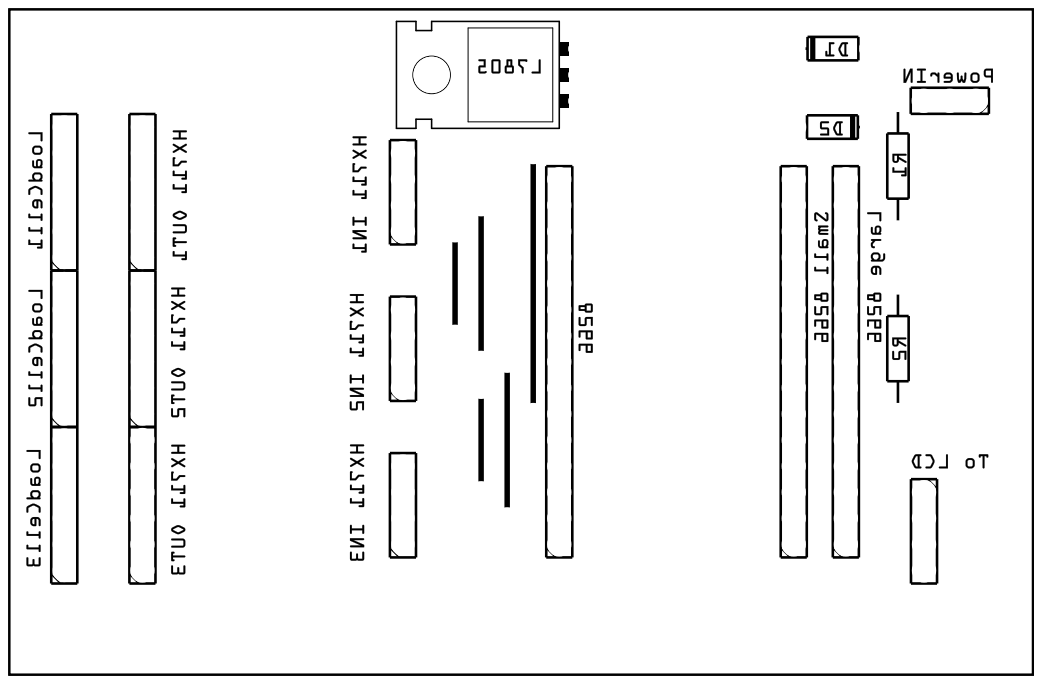
[picture p99: page 1]
