nightflyer88/CG_scale/Doc/Balance CPT 5mm/img/20200418_210656.jpg

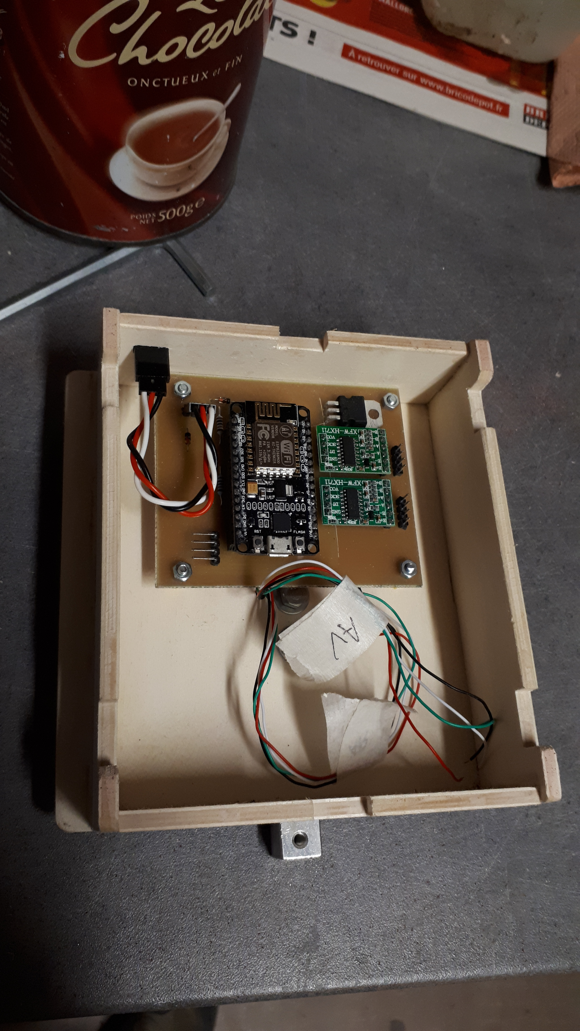
Doc/Balance CPT 5mm/img/20200418_210656.jpg
